RhythmSyed/HMD/NativeBase-KitchenSink-master/assets/contacts/sankhadeep.png

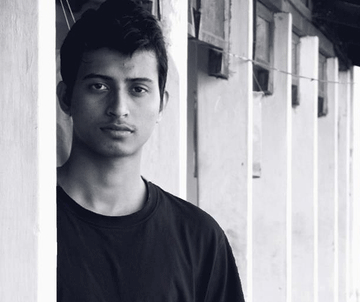
NativeBase-KitchenSink-master/assets/contacts/sankhadeep.png
