RhythmSyed/HMD/NativeBase-KitchenSink-master/assets/contacts/saurabh.png

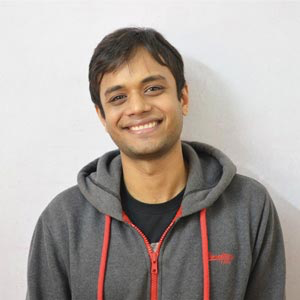
NativeBase-KitchenSink-master/assets/contacts/saurabh.png
