RhythmSyed/HMD/mobileProject/ios/Pods/GoogleMaps/Example/GoogleMapsDemos/Resources/australia-large@2x.png

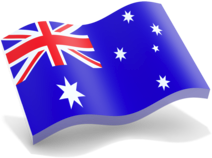
mobileProject/ios/Pods/GoogleMaps/Example/GoogleMapsDemos/Resources/australia-large@2x.png
