RhythmSyed/HMD/mobileProject/ios/Pods/GoogleMaps/Example/GoogleMapsDemos/Resources/newark_nj_1922.jpg

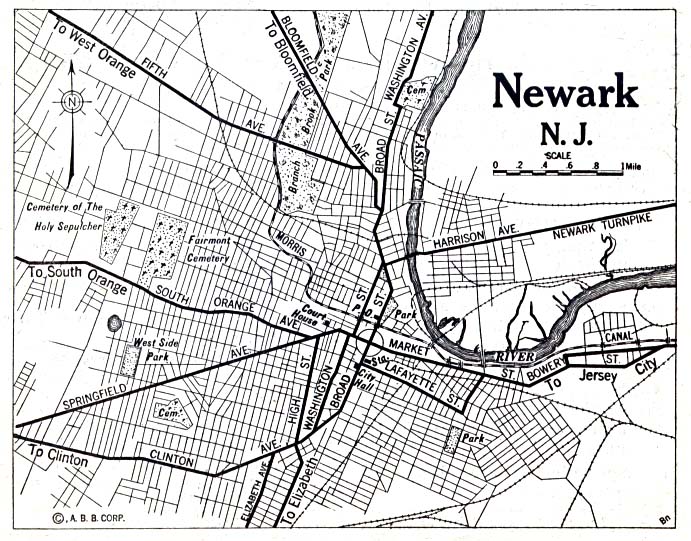
mobileProject/ios/Pods/GoogleMaps/Example/GoogleMapsDemos/Resources/newark_nj_1922.jpg
