RhythmSyed/HMD/NativeBase-KitchenSink-master/assets/camera.png

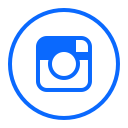
NativeBase-KitchenSink-master/assets/camera.png
