RhythmSyed/HMD/NativeBase-KitchenSink-master/assets/contacts/atul.png

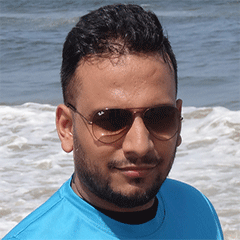
NativeBase-KitchenSink-master/assets/contacts/atul.png
