RhythmSyed/HMD/NativeBase-KitchenSink-master/assets/contacts/himanshu.png

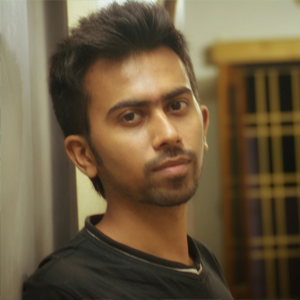
NativeBase-KitchenSink-master/assets/contacts/himanshu.png
