RhythmSyed/HMD/NativeBase-KitchenSink-master/assets/contacts/megha.png

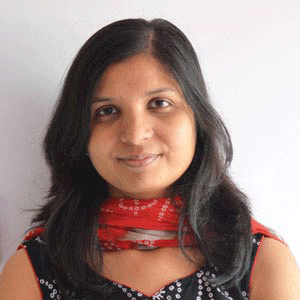
NativeBase-KitchenSink-master/assets/contacts/megha.png
