RhythmSyed/HMD/NativeBase-KitchenSink-master/assets/contacts/pratik.png

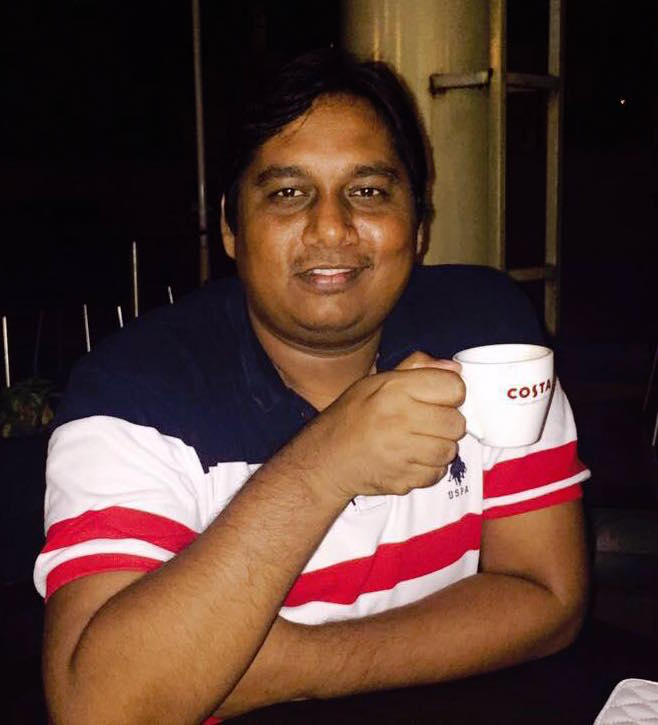
NativeBase-KitchenSink-master/assets/contacts/pratik.png
