RhythmSyed/HMD/NativeBase-KitchenSink-master/assets/contacts/sanket.png

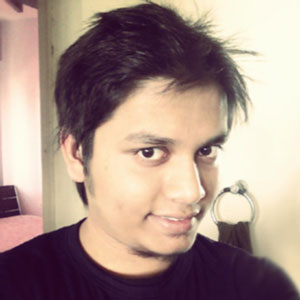
NativeBase-KitchenSink-master/assets/contacts/sanket.png
