RhythmSyed/HMD/NativeBase-KitchenSink-master/assets/contacts/shivraj.png

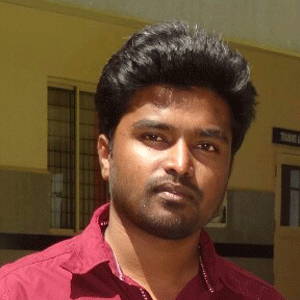
NativeBase-KitchenSink-master/assets/contacts/shivraj.png
