RhythmSyed/HMD/NativeBase-KitchenSink-master/assets/contacts/shruti.png

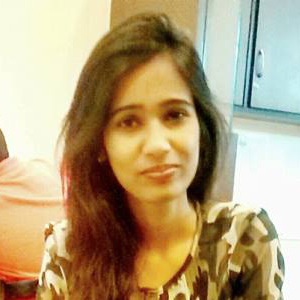
NativeBase-KitchenSink-master/assets/contacts/shruti.png
