RhythmSyed/HMD/NativeBase-KitchenSink-master/assets/contacts/shweta.png

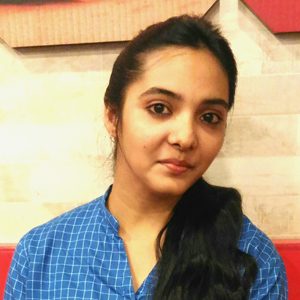
NativeBase-KitchenSink-master/assets/contacts/shweta.png
