RhythmSyed/HMD/NativeBase-KitchenSink-master/assets/contacts/supriya.png

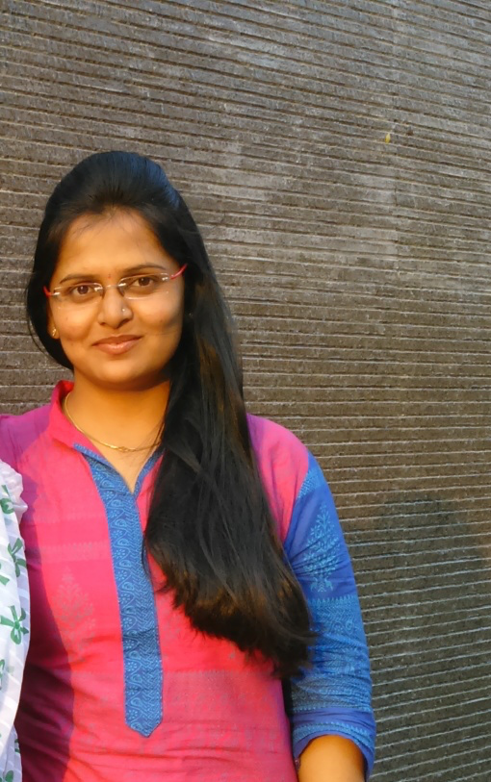
NativeBase-KitchenSink-master/assets/contacts/supriya.png
