RhythmSyed/HMD/NativeBase-KitchenSink-master/assets/contacts/varun.png

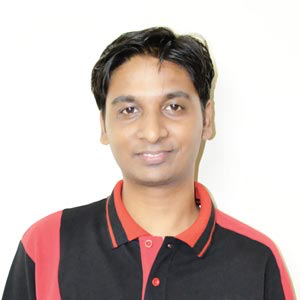
NativeBase-KitchenSink-master/assets/contacts/varun.png
