RhythmSyed/HMD/NativeBase-KitchenSink-master/assets/drawer-cover.png

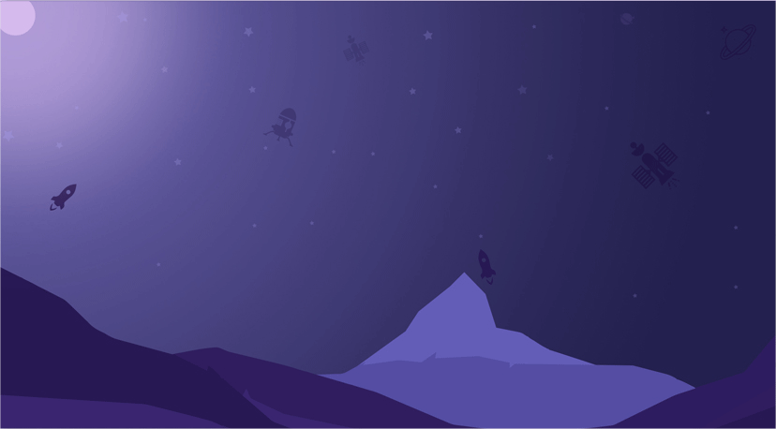
NativeBase-KitchenSink-master/assets/drawer-cover.png
