RhythmSyed/HMD/NativeBase-KitchenSink-master/assets/header-transparent.png

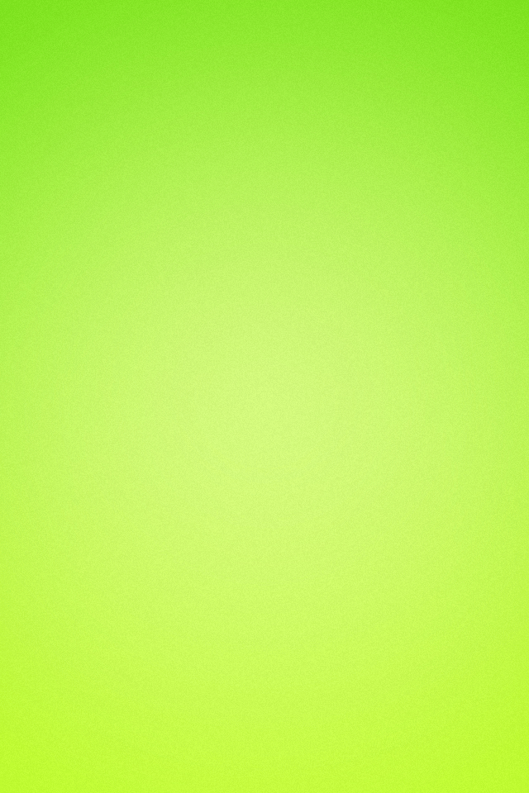
NativeBase-KitchenSink-master/assets/header-transparent.png
