RhythmSyed/HMD/NativeBase-KitchenSink-master/assets/launchscreen-bg.png

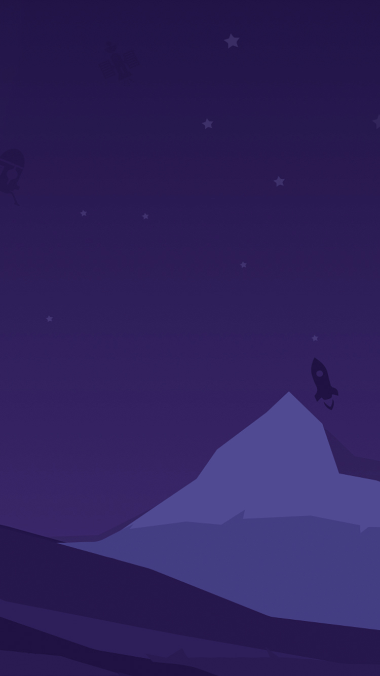
NativeBase-KitchenSink-master/assets/launchscreen-bg.png
