RhythmSyed/HMD/NativeBase-KitchenSink-master/assets/swiper-1.png

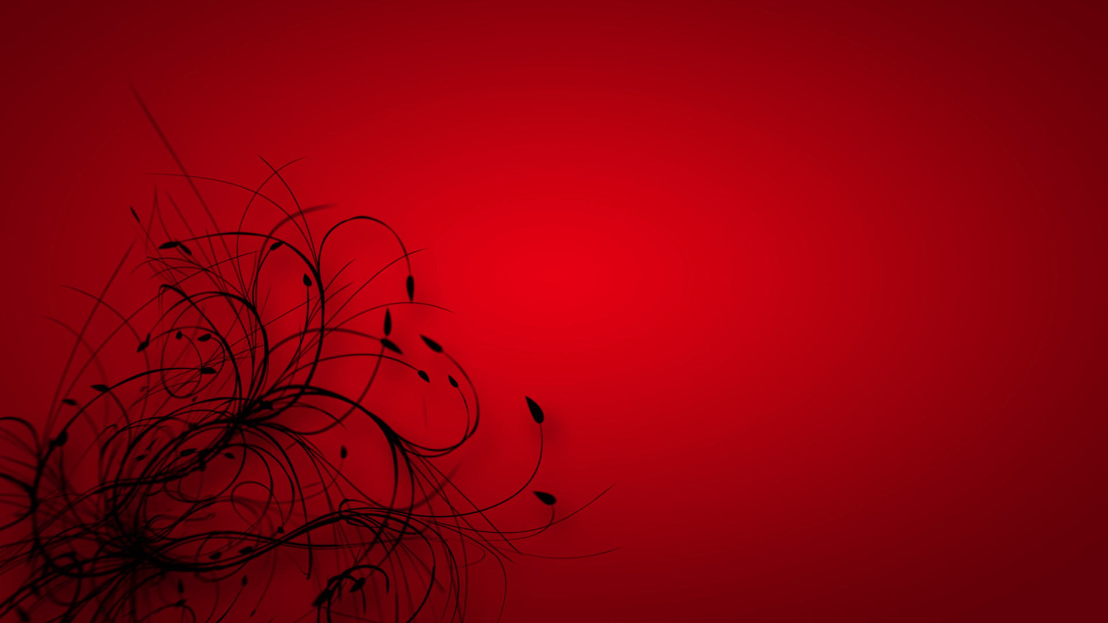
NativeBase-KitchenSink-master/assets/swiper-1.png
