RhythmSyed/HMD/NativeBase-KitchenSink-master/assets/swiper-3.png

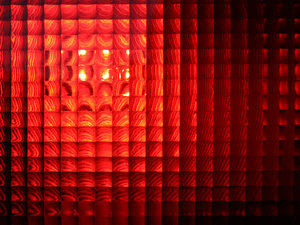
NativeBase-KitchenSink-master/assets/swiper-3.png
