RhythmSyed/HMD/NativeBase-KitchenSink-master/assets/swiper-4.png

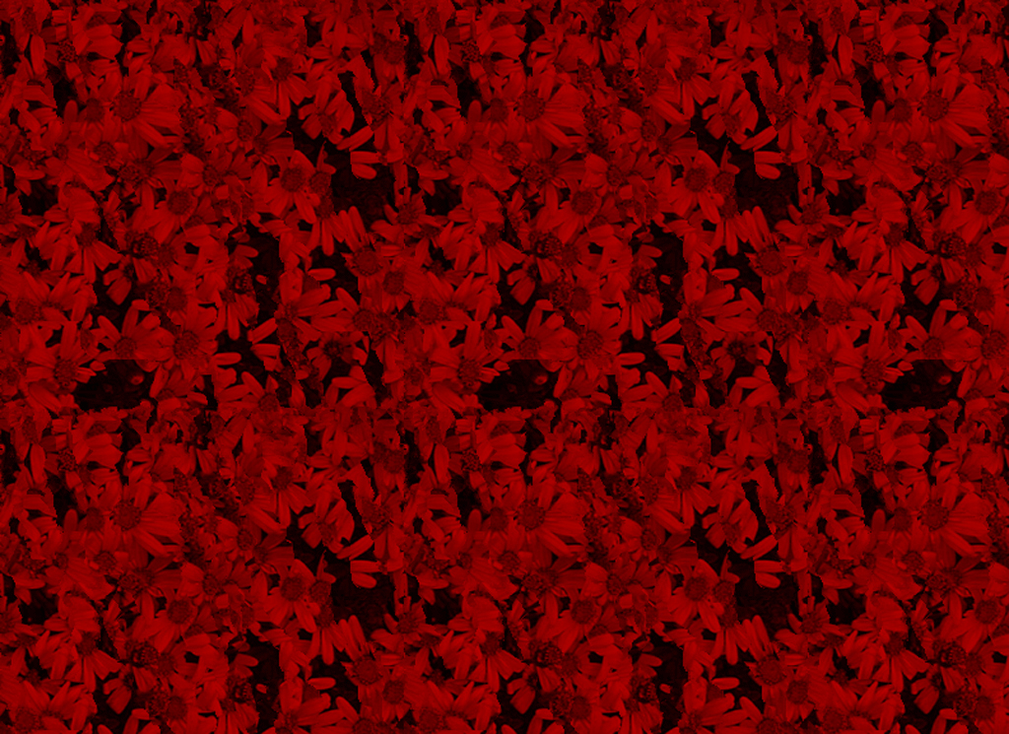
NativeBase-KitchenSink-master/assets/swiper-4.png
