RhythmSyed/HMD/NativeBase-KitchenSink-master/assets/web-cover1.png

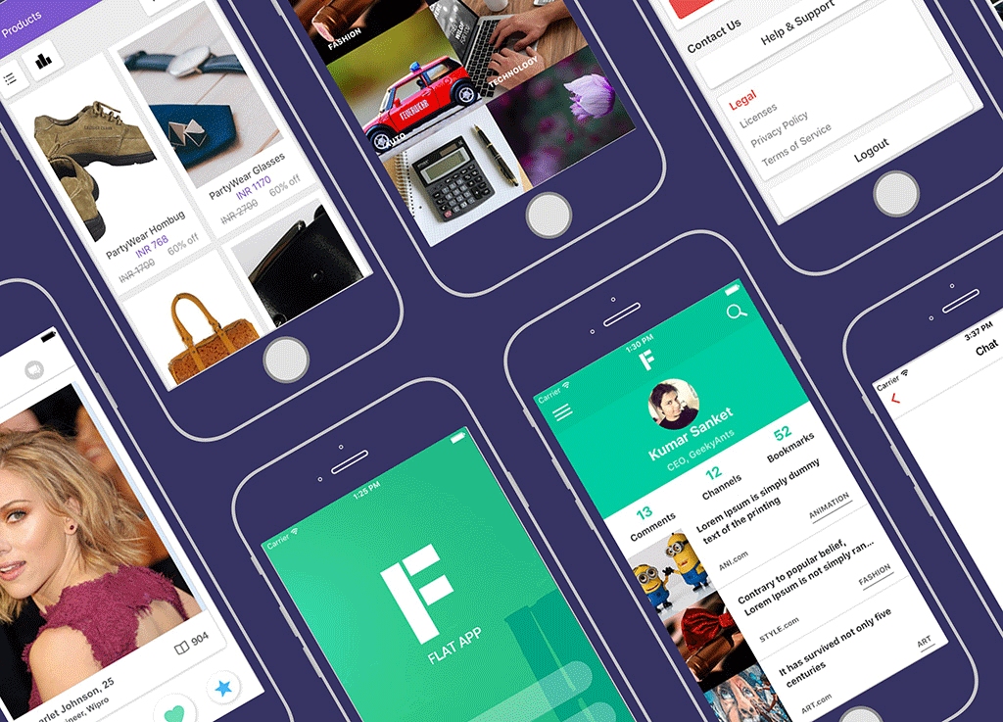
NativeBase-KitchenSink-master/assets/web-cover1.png
