RhythmSyed/HMD/NativeBase-KitchenSink-master/screenshots/Android.gif

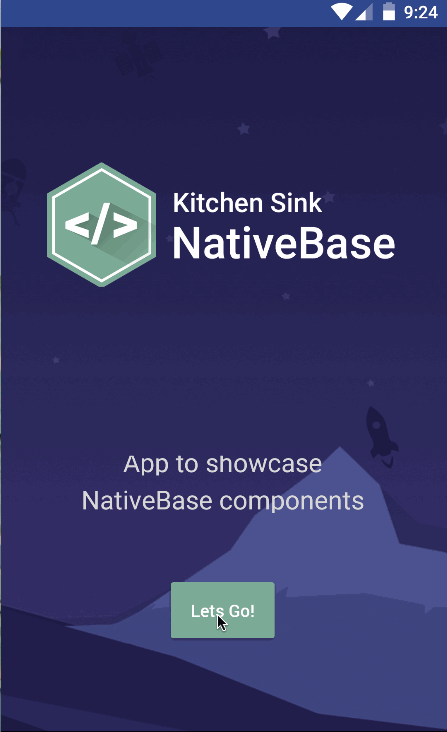
NativeBase-KitchenSink-master/screenshots/Android.gif
