RhythmSyed/HMD/NativeBase-KitchenSink-master/screenshots/android/accordion-custom-header-content.gif

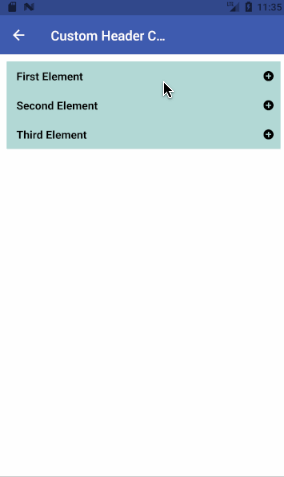
NativeBase-KitchenSink-master/screenshots/android/accordion-custom-header-content.gif
