RhythmSyed/HMD/NativeBase-KitchenSink-master/screenshots/android/accordion-header-content-style.gif

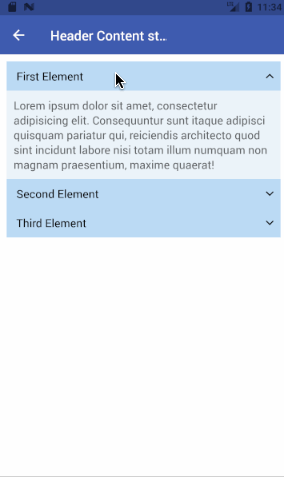
NativeBase-KitchenSink-master/screenshots/android/accordion-header-content-style.gif
