RhythmSyed/HMD/NativeBase-KitchenSink-master/screenshots/android/accordion.gif

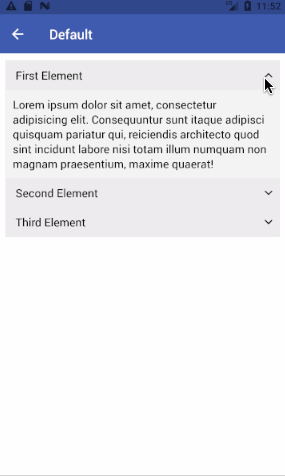
NativeBase-KitchenSink-master/screenshots/android/accordion.gif
