RhythmSyed/HMD/NativeBase-KitchenSink-master/screenshots/android/actionsheet.gif

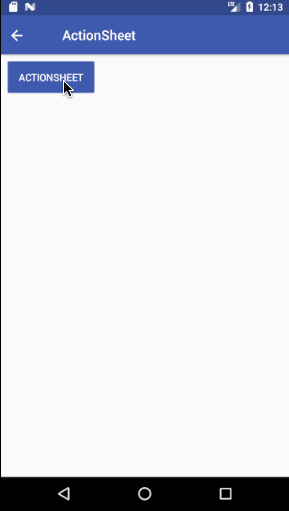
NativeBase-KitchenSink-master/screenshots/android/actionsheet.gif
