RhythmSyed/HMD/NativeBase-KitchenSink-master/screenshots/android/anatomy.png

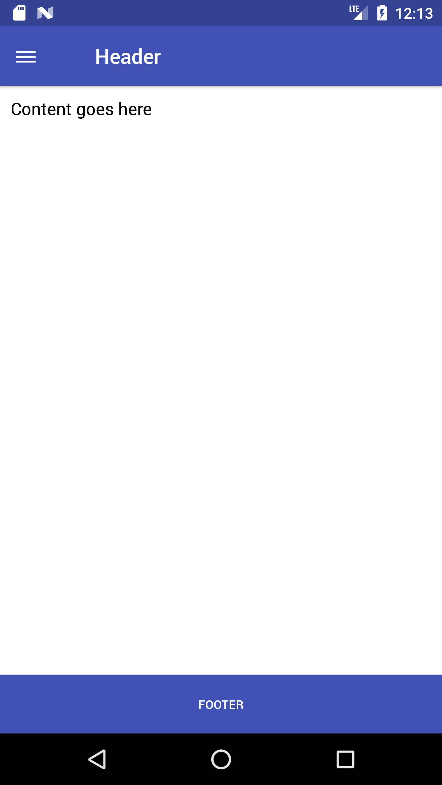
NativeBase-KitchenSink-master/screenshots/android/anatomy.png
