RhythmSyed/HMD/NativeBase-KitchenSink-master/screenshots/android/button-block.png

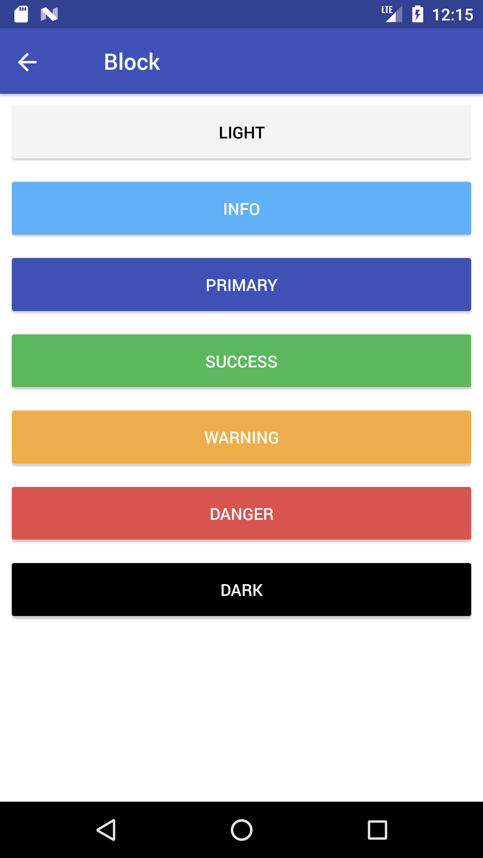
NativeBase-KitchenSink-master/screenshots/android/button-block.png
