RhythmSyed/HMD/NativeBase-KitchenSink-master/screenshots/android/button-disabled.png

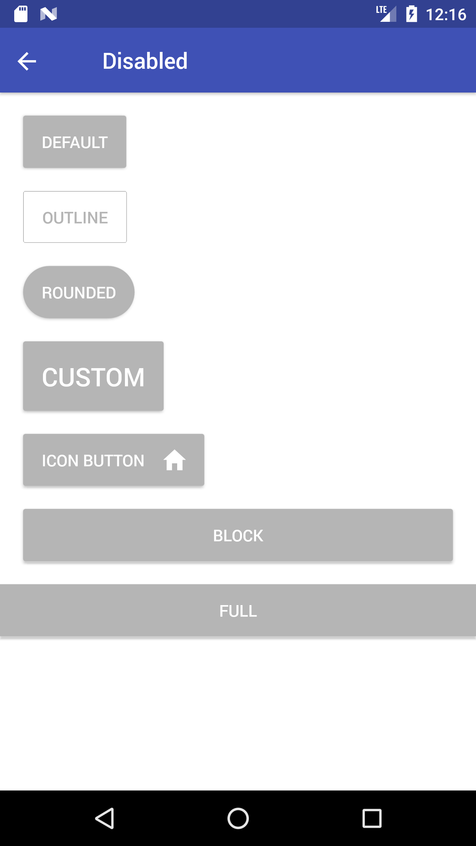
NativeBase-KitchenSink-master/screenshots/android/button-disabled.png
