RhythmSyed/HMD/NativeBase-KitchenSink-master/screenshots/android/button-full.png

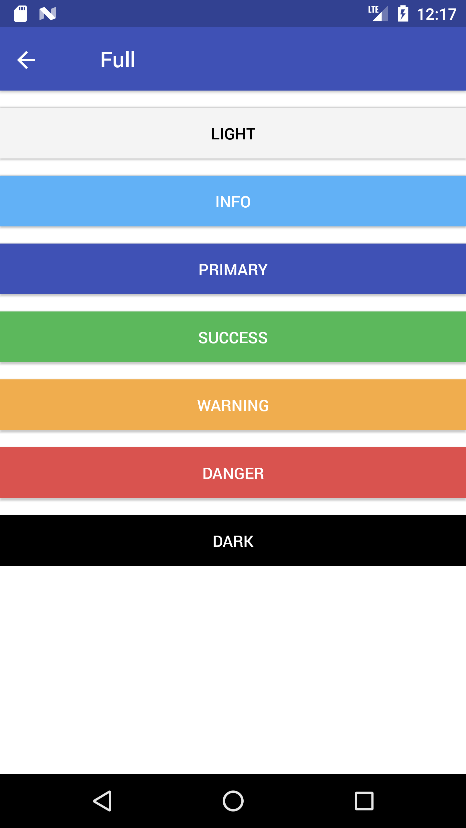
NativeBase-KitchenSink-master/screenshots/android/button-full.png
