RhythmSyed/HMD/NativeBase-KitchenSink-master/screenshots/android/button-outline.png

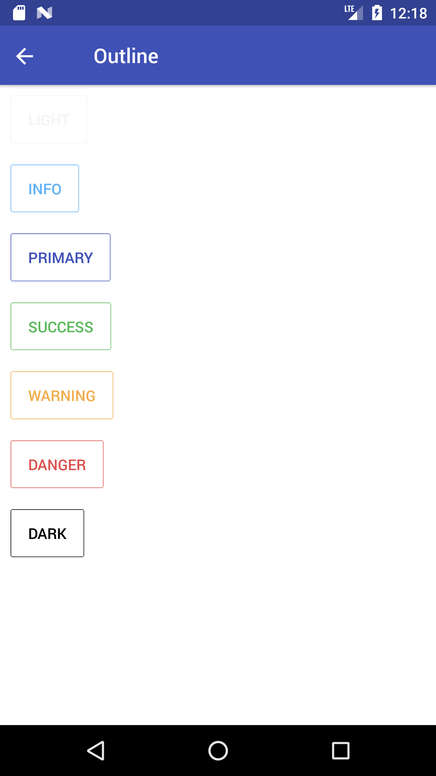
NativeBase-KitchenSink-master/screenshots/android/button-outline.png
