RhythmSyed/HMD/NativeBase-KitchenSink-master/screenshots/android/button-size.png

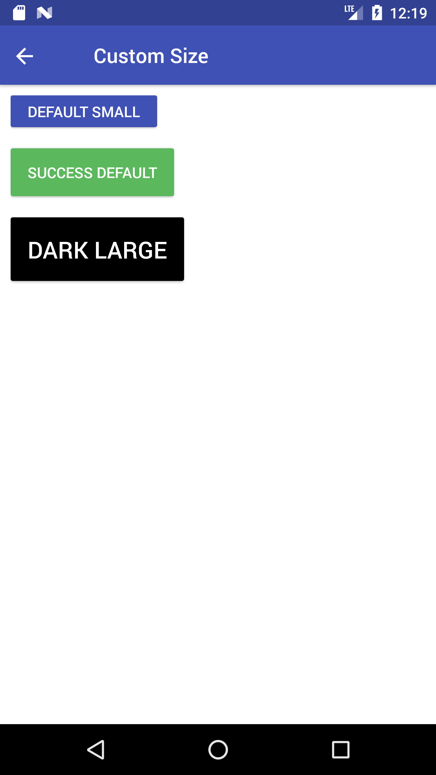
NativeBase-KitchenSink-master/screenshots/android/button-size.png
