RhythmSyed/HMD/NativeBase-KitchenSink-master/screenshots/android/button-transparent.png

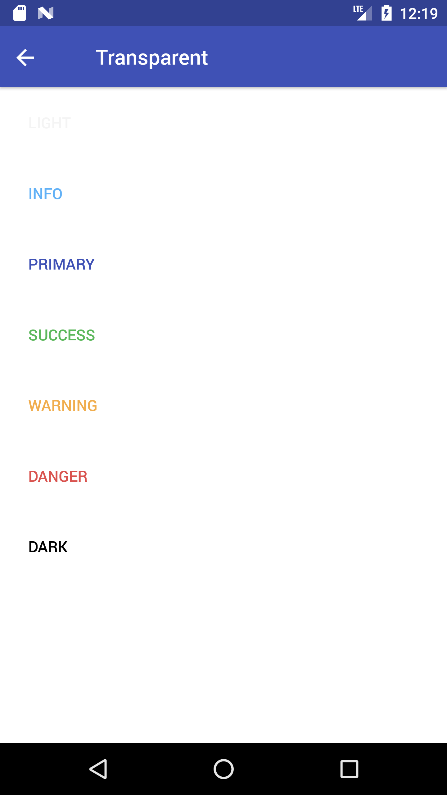
NativeBase-KitchenSink-master/screenshots/android/button-transparent.png
