RhythmSyed/HMD/NativeBase-KitchenSink-master/screenshots/android/card-basic.png

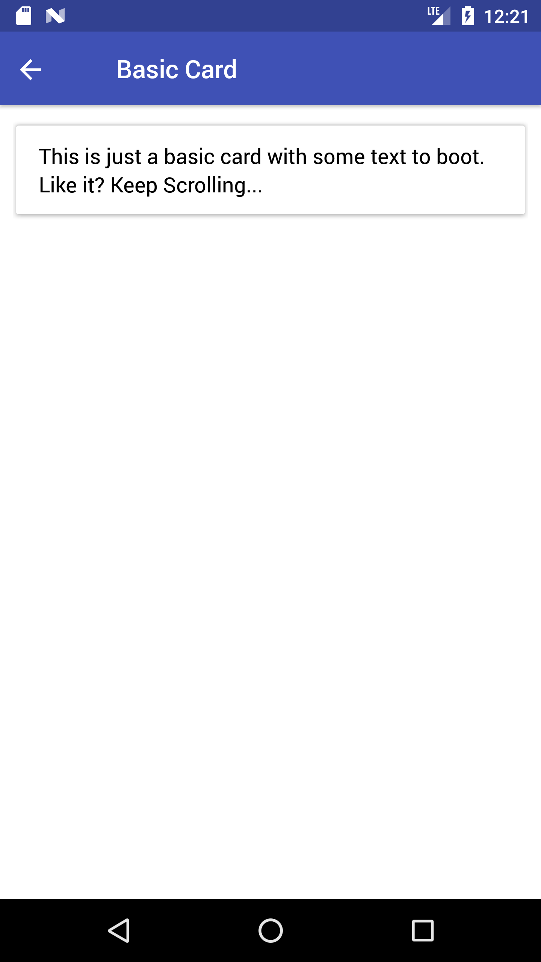
NativeBase-KitchenSink-master/screenshots/android/card-basic.png
