RhythmSyed/HMD/NativeBase-KitchenSink-master/screenshots/android/card-bordered.png

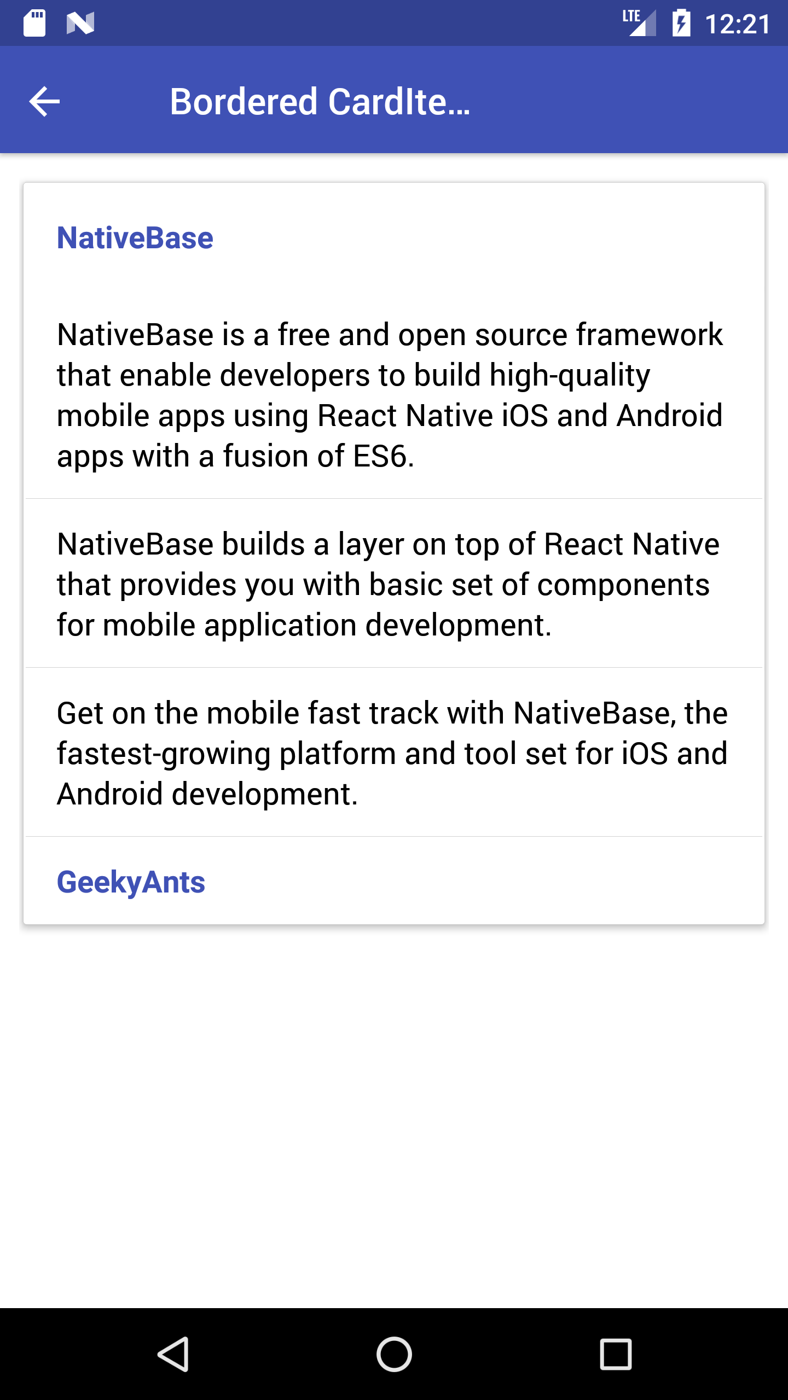
NativeBase-KitchenSink-master/screenshots/android/card-bordered.png
