RhythmSyed/HMD/NativeBase-KitchenSink-master/screenshots/android/card-button.gif

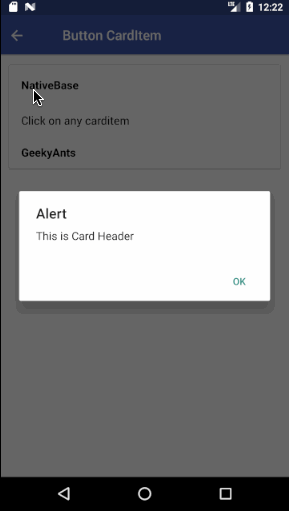
NativeBase-KitchenSink-master/screenshots/android/card-button.gif
