RhythmSyed/HMD/NativeBase-KitchenSink-master/screenshots/android/card-custom-border-radius.png

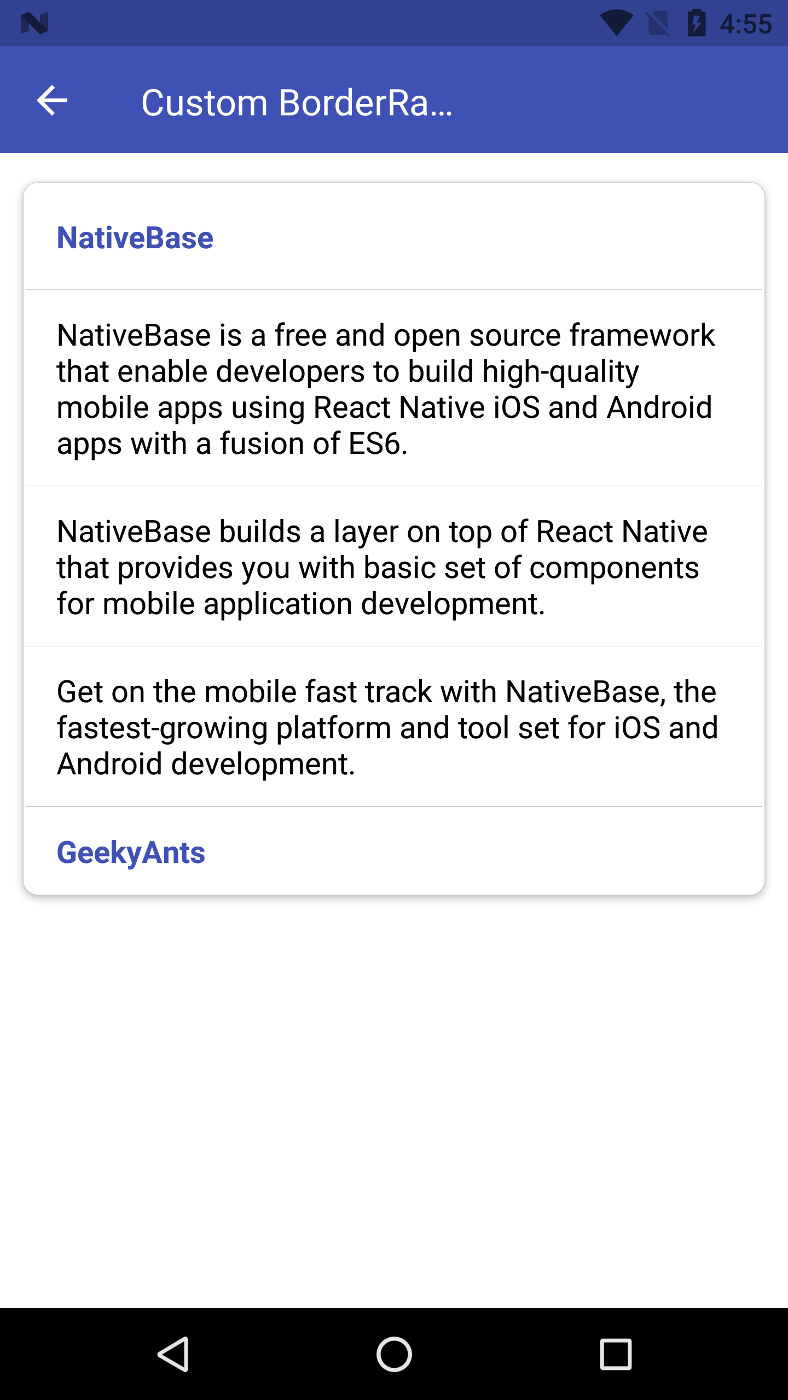
NativeBase-KitchenSink-master/screenshots/android/card-custom-border-radius.png
