RhythmSyed/HMD/NativeBase-KitchenSink-master/screenshots/android/card-image.png

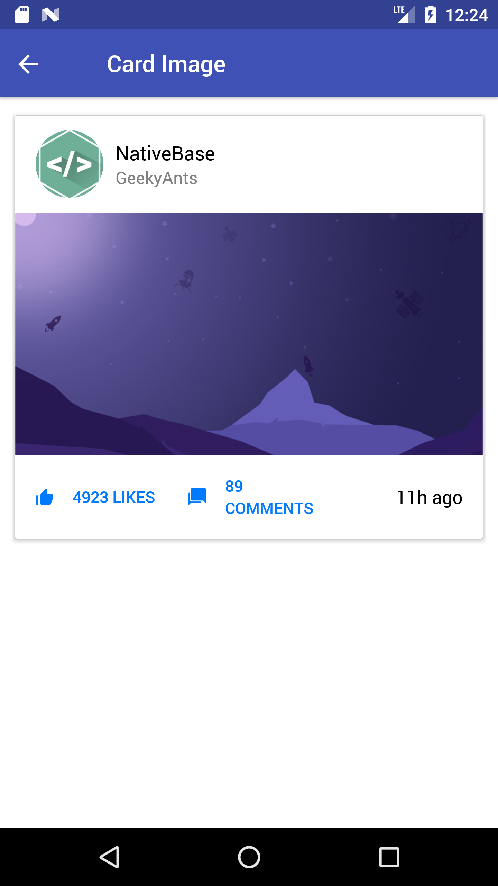
NativeBase-KitchenSink-master/screenshots/android/card-image.png
