RhythmSyed/HMD/NativeBase-KitchenSink-master/screenshots/android/card-list.png

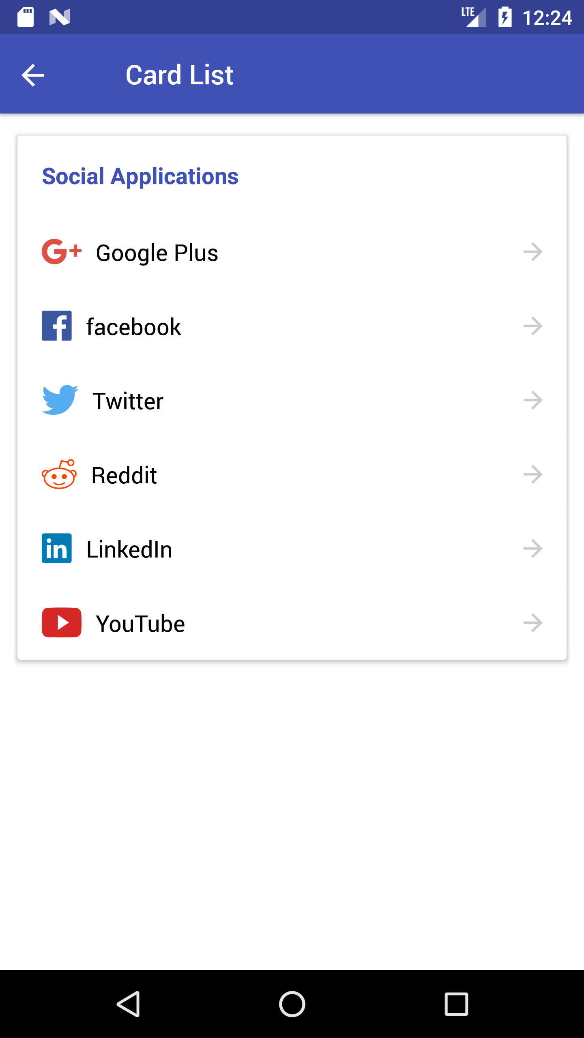
NativeBase-KitchenSink-master/screenshots/android/card-list.png
