RhythmSyed/HMD/NativeBase-KitchenSink-master/screenshots/android/card-showcase.png

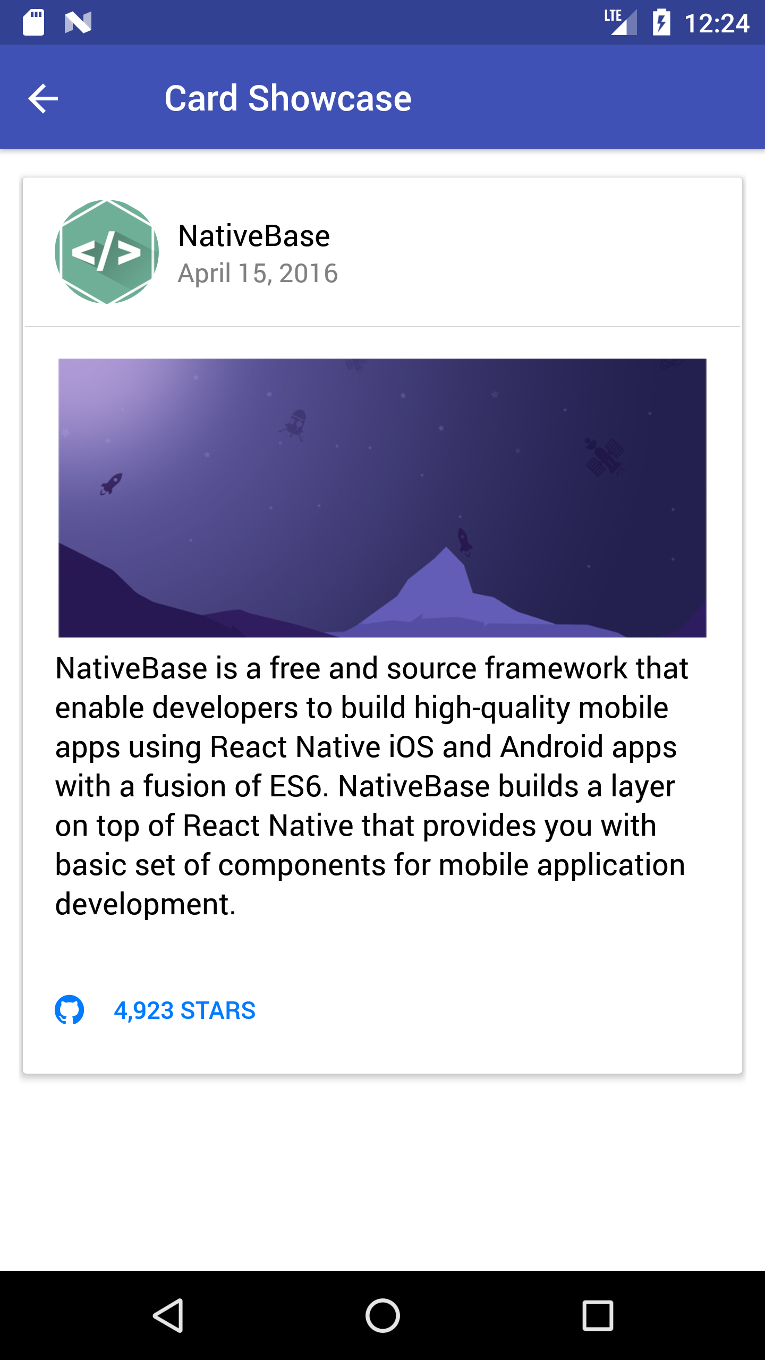
NativeBase-KitchenSink-master/screenshots/android/card-showcase.png
