RhythmSyed/HMD/NativeBase-KitchenSink-master/screenshots/android/card-transparent.png

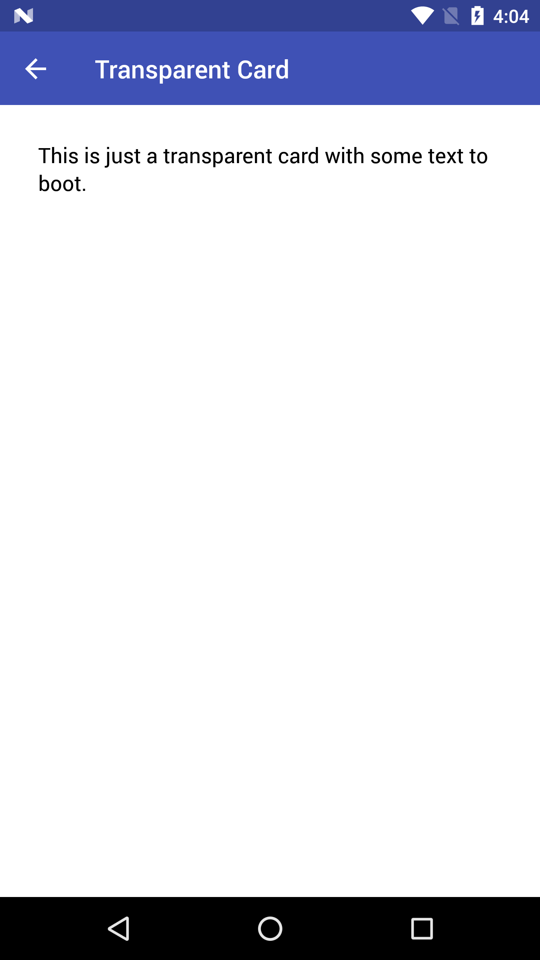
NativeBase-KitchenSink-master/screenshots/android/card-transparent.png
