RhythmSyed/HMD/NativeBase-KitchenSink-master/screenshots/android/checkbox.png

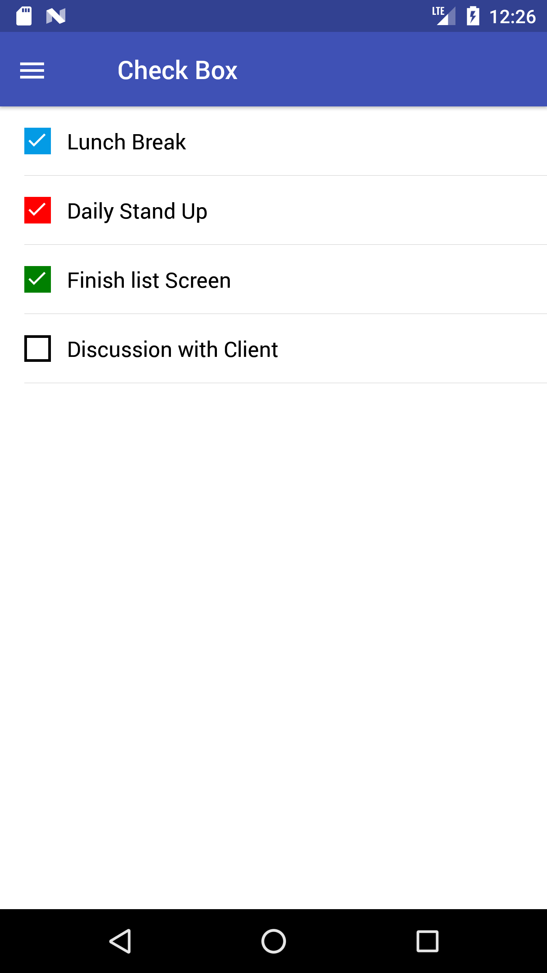
NativeBase-KitchenSink-master/screenshots/android/checkbox.png
