RhythmSyed/HMD/NativeBase-KitchenSink-master/screenshots/android/deckswiper-advanced.gif

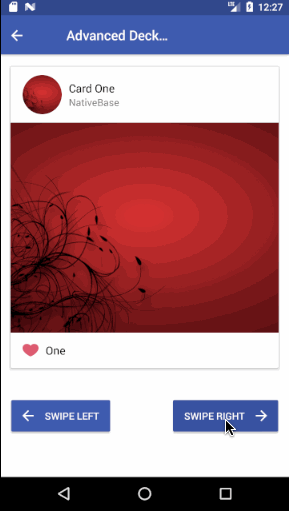
NativeBase-KitchenSink-master/screenshots/android/deckswiper-advanced.gif
