RhythmSyed/HMD/NativeBase-KitchenSink-master/screenshots/android/deckswiper.gif

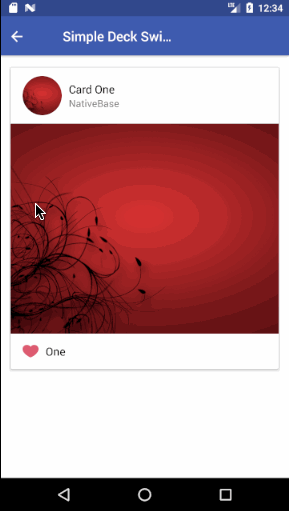
NativeBase-KitchenSink-master/screenshots/android/deckswiper.gif
