RhythmSyed/HMD/NativeBase-KitchenSink-master/screenshots/android/drawer.png

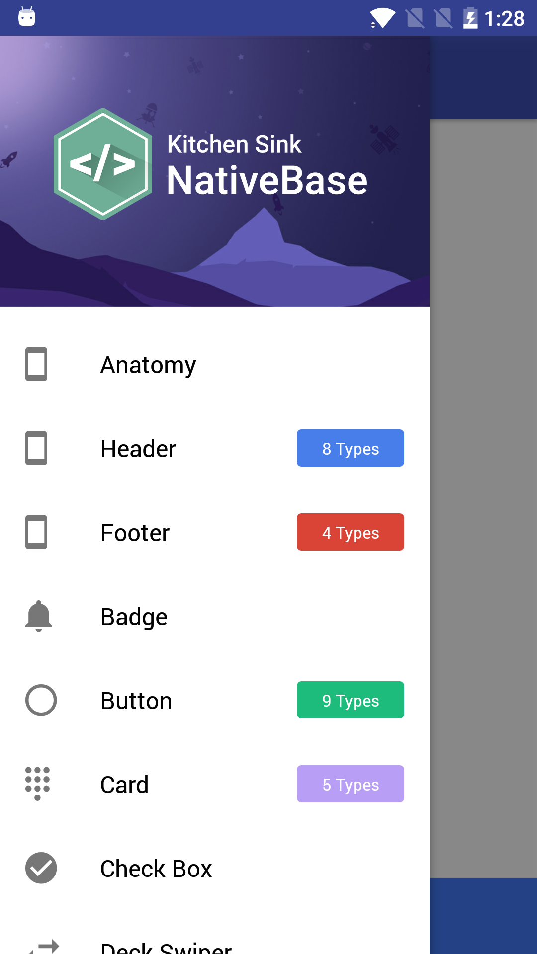
NativeBase-KitchenSink-master/screenshots/android/drawer.png
