RhythmSyed/HMD/NativeBase-KitchenSink-master/screenshots/android/FAB-multiple.gif

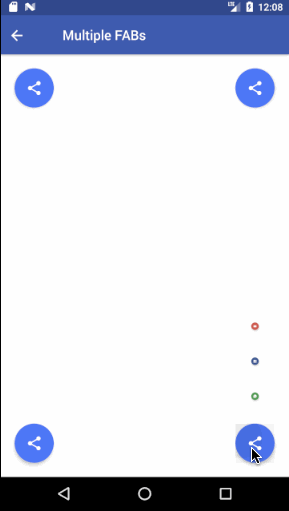
NativeBase-KitchenSink-master/screenshots/android/FAB-multiple.gif
