RhythmSyed/HMD/NativeBase-KitchenSink-master/screenshots/android/FAB-single.gif

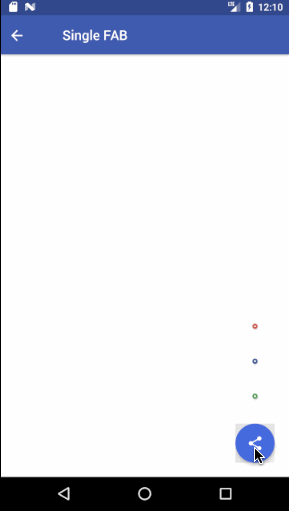
NativeBase-KitchenSink-master/screenshots/android/FAB-single.gif
