RhythmSyed/HMD/NativeBase-KitchenSink-master/screenshots/android/footer-text.png

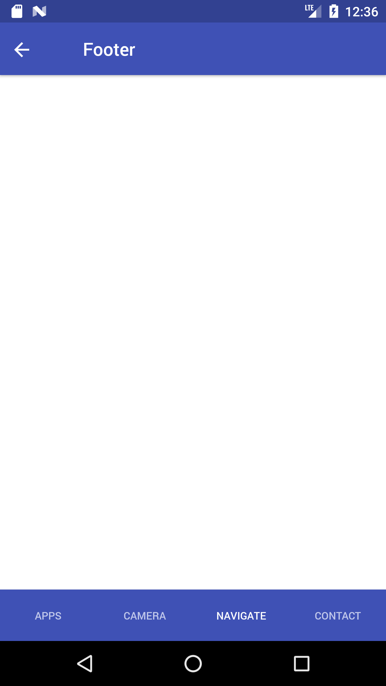
NativeBase-KitchenSink-master/screenshots/android/footer-text.png
