RhythmSyed/HMD/NativeBase-KitchenSink-master/screenshots/android/header-custom.png

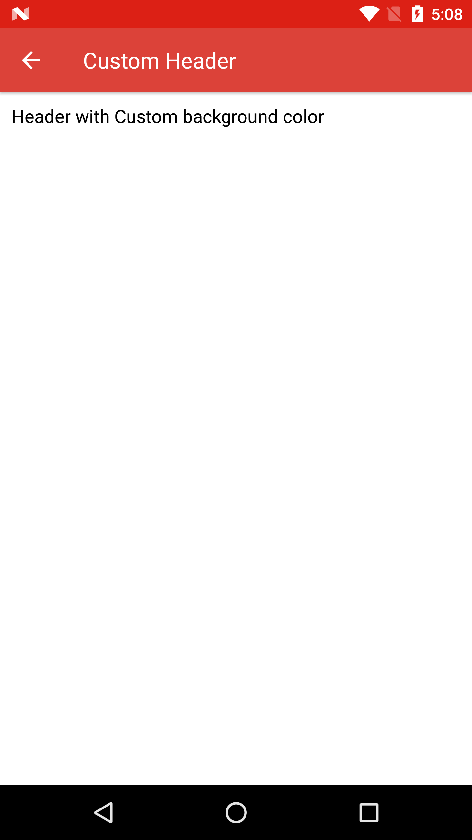
NativeBase-KitchenSink-master/screenshots/android/header-custom.png
