RhythmSyed/HMD/NativeBase-KitchenSink-master/screenshots/android/header-noleft.png

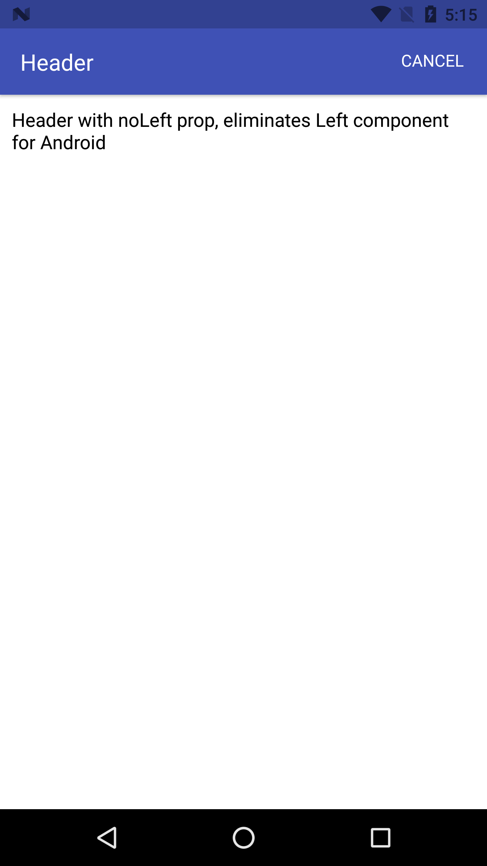
NativeBase-KitchenSink-master/screenshots/android/header-noleft.png
