RhythmSyed/HMD/NativeBase-KitchenSink-master/screenshots/android/header-noshadow.png

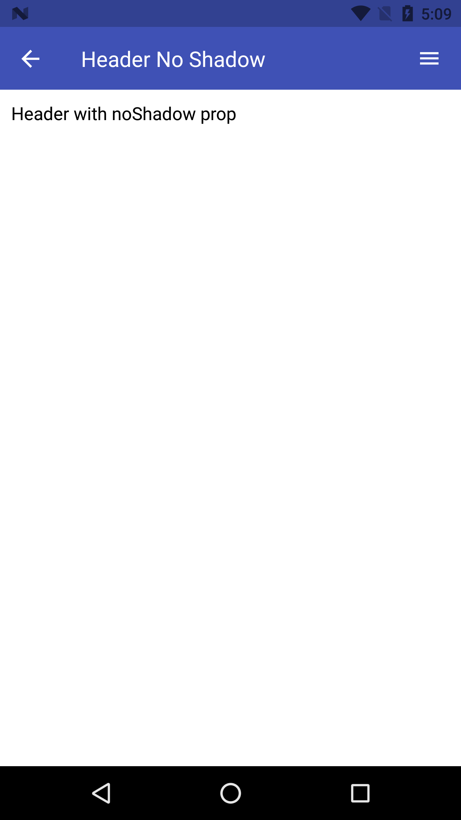
NativeBase-KitchenSink-master/screenshots/android/header-noshadow.png
