RhythmSyed/HMD/NativeBase-KitchenSink-master/screenshots/android/header-span.png

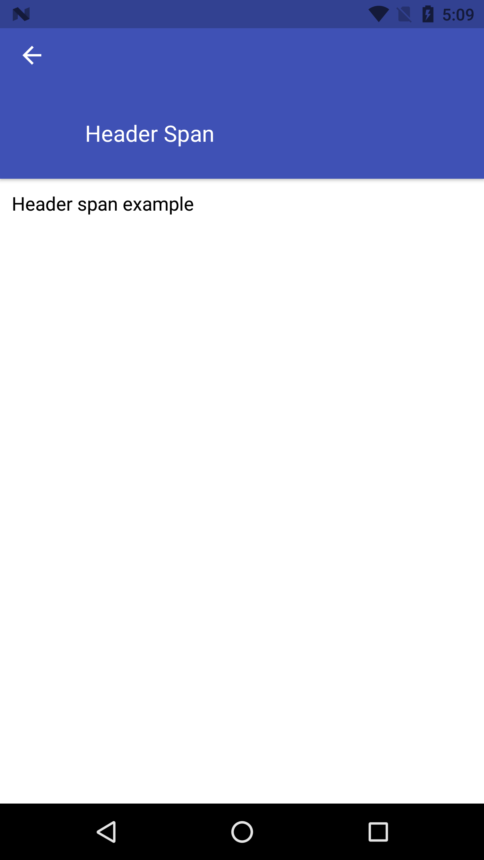
NativeBase-KitchenSink-master/screenshots/android/header-span.png
