RhythmSyed/HMD/NativeBase-KitchenSink-master/screenshots/android/header-with-title.png

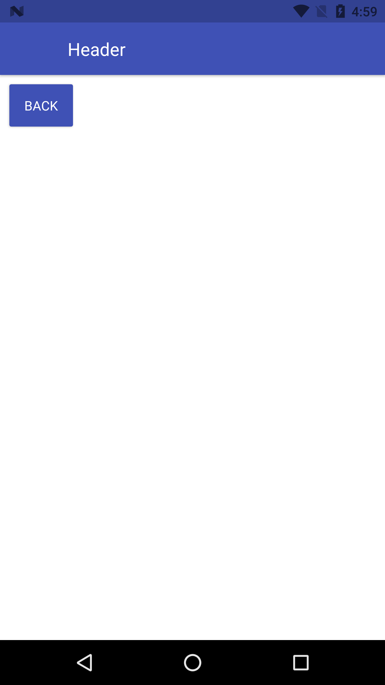
NativeBase-KitchenSink-master/screenshots/android/header-with-title.png
