RhythmSyed/HMD/NativeBase-KitchenSink-master/screenshots/android/input-fixed.png

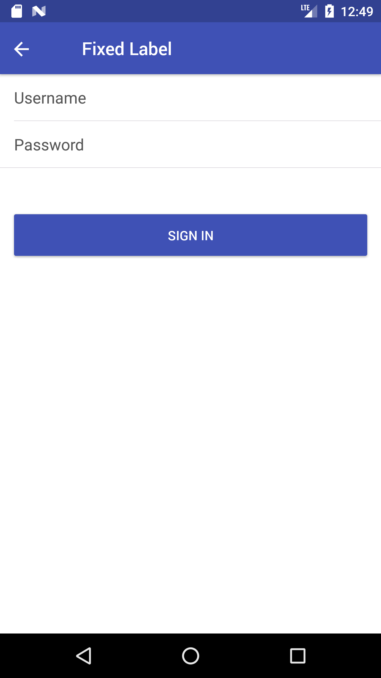
NativeBase-KitchenSink-master/screenshots/android/input-fixed.png
