RhythmSyed/HMD/NativeBase-KitchenSink-master/screenshots/android/input-floating.gif

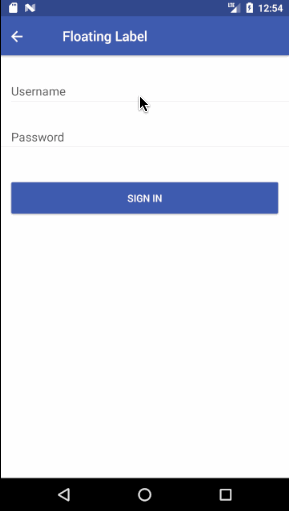
NativeBase-KitchenSink-master/screenshots/android/input-floating.gif
