RhythmSyed/HMD/NativeBase-KitchenSink-master/screenshots/android/input-picker.gif

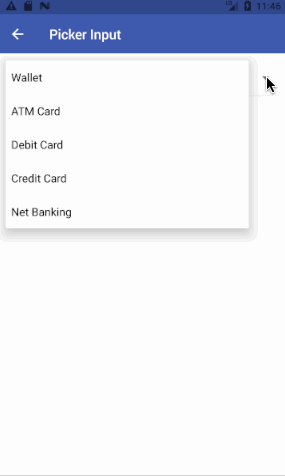
NativeBase-KitchenSink-master/screenshots/android/input-picker.gif
