RhythmSyed/HMD/NativeBase-KitchenSink-master/screenshots/android/layout.png

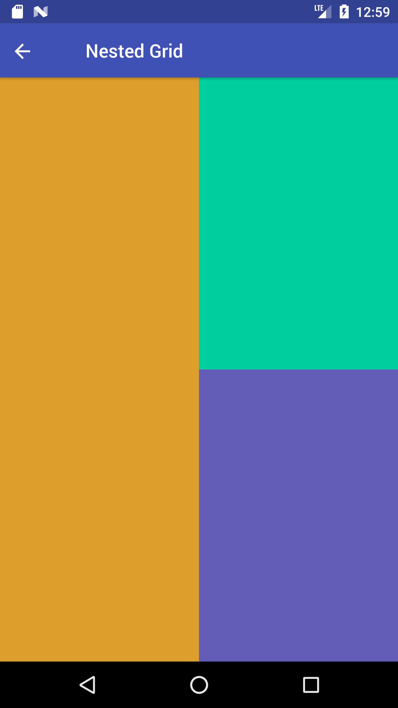
NativeBase-KitchenSink-master/screenshots/android/layout.png
