RhythmSyed/HMD/NativeBase-KitchenSink-master/screenshots/android/list-basic.png

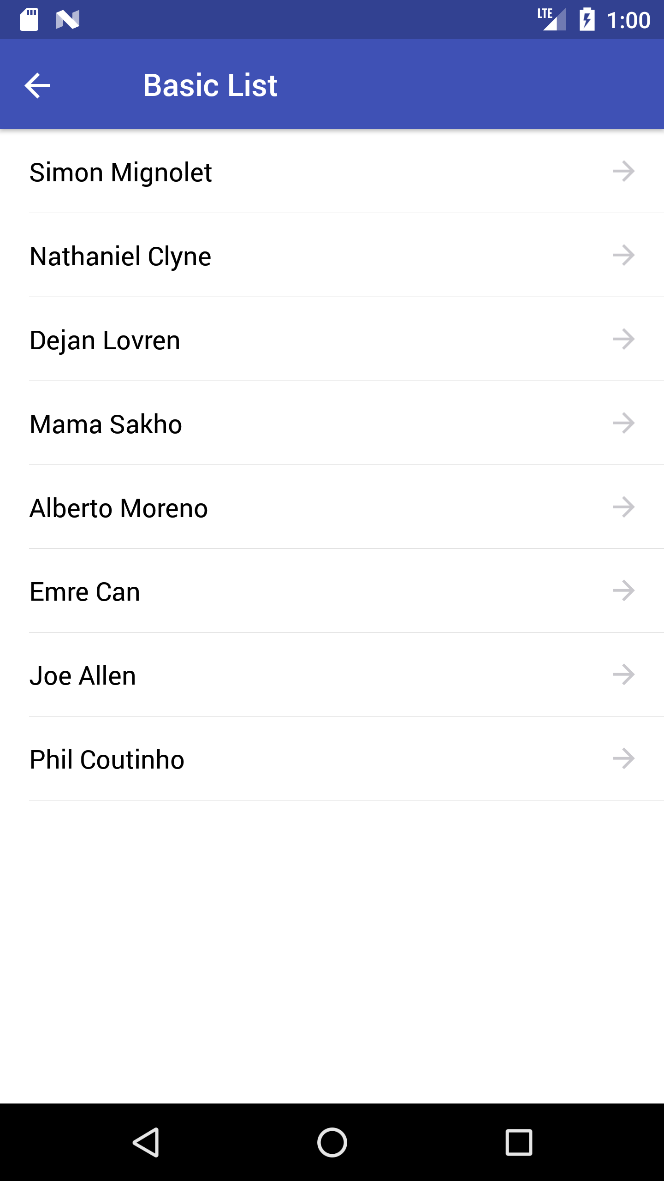
NativeBase-KitchenSink-master/screenshots/android/list-basic.png
