RhythmSyed/HMD/NativeBase-KitchenSink-master/screenshots/android/list-divider.png

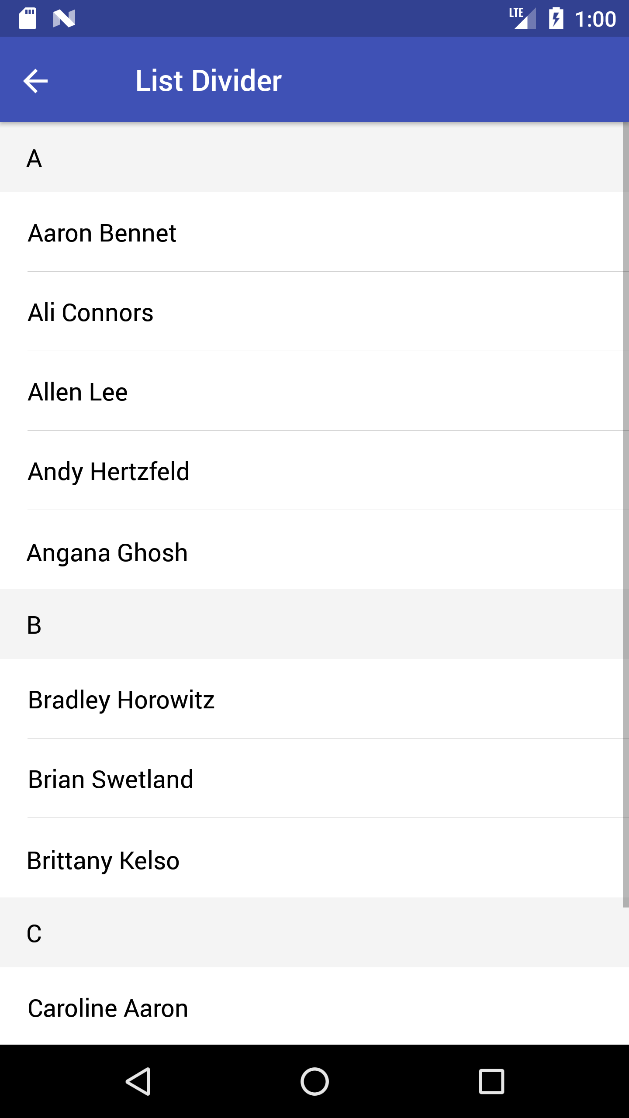
NativeBase-KitchenSink-master/screenshots/android/list-divider.png
