RhythmSyed/HMD/NativeBase-KitchenSink-master/screenshots/android/list-dynamic.png

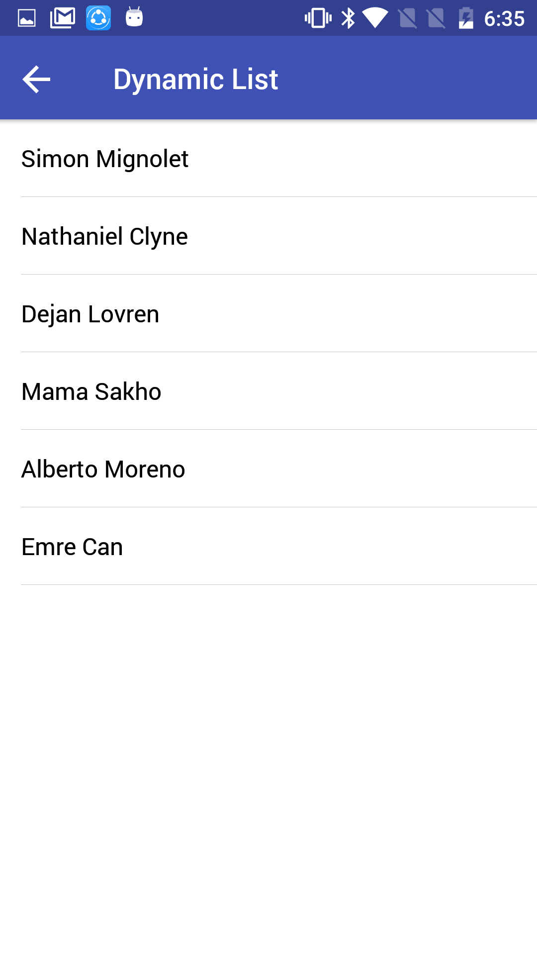
NativeBase-KitchenSink-master/screenshots/android/list-dynamic.png
