RhythmSyed/HMD/NativeBase-KitchenSink-master/screenshots/android/list-header.png

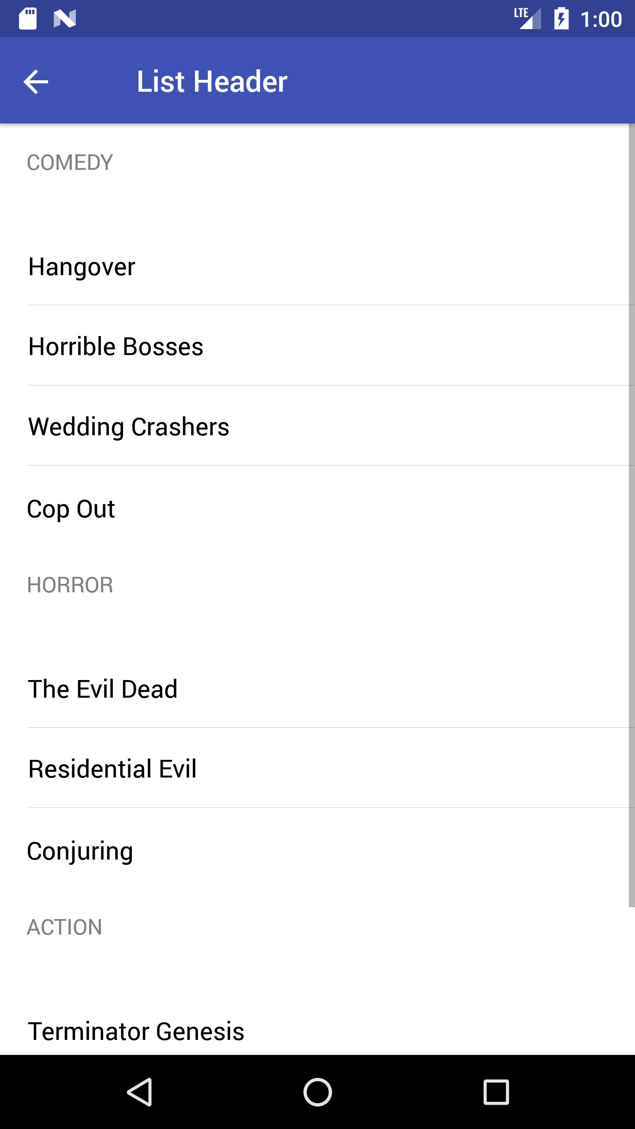
NativeBase-KitchenSink-master/screenshots/android/list-header.png
