RhythmSyed/HMD/NativeBase-KitchenSink-master/screenshots/android/list-separator.png

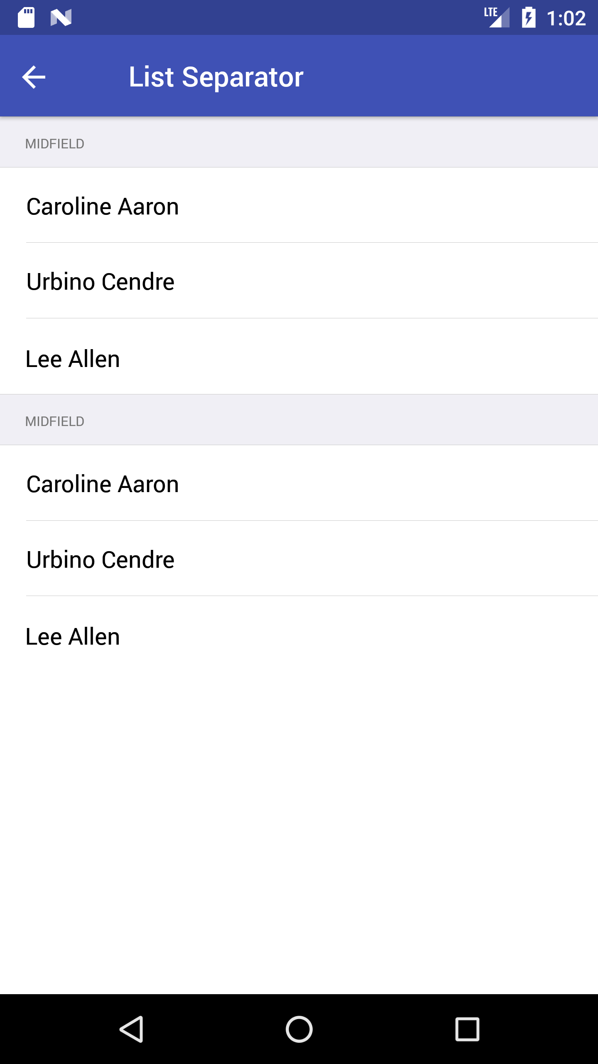
NativeBase-KitchenSink-master/screenshots/android/list-separator.png
