RhythmSyed/HMD/NativeBase-KitchenSink-master/screenshots/android/list-swipe-multiple.gif

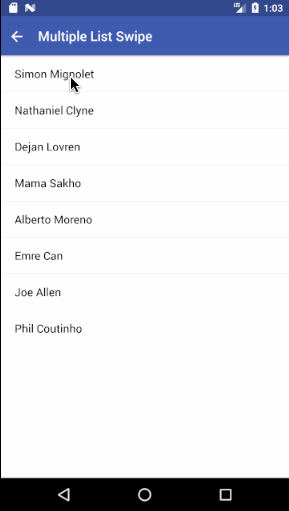
NativeBase-KitchenSink-master/screenshots/android/list-swipe-multiple.gif
