RhythmSyed/HMD/NativeBase-KitchenSink-master/screenshots/android/list-swipe-single-row-custom-style.gif

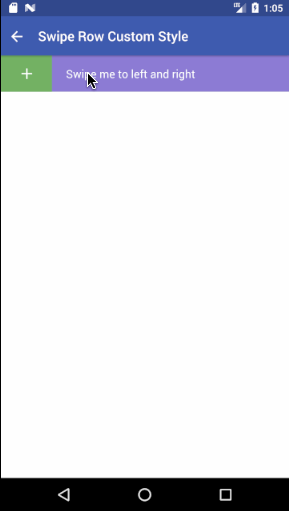
NativeBase-KitchenSink-master/screenshots/android/list-swipe-single-row-custom-style.gif
