RhythmSyed/HMD/NativeBase-KitchenSink-master/screenshots/android/list-swipe-single-row.gif

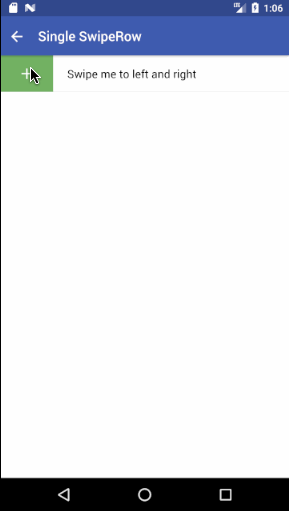
NativeBase-KitchenSink-master/screenshots/android/list-swipe-single-row.gif
