RhythmSyed/HMD/NativeBase-KitchenSink-master/screenshots/android/list-thumbnail.png

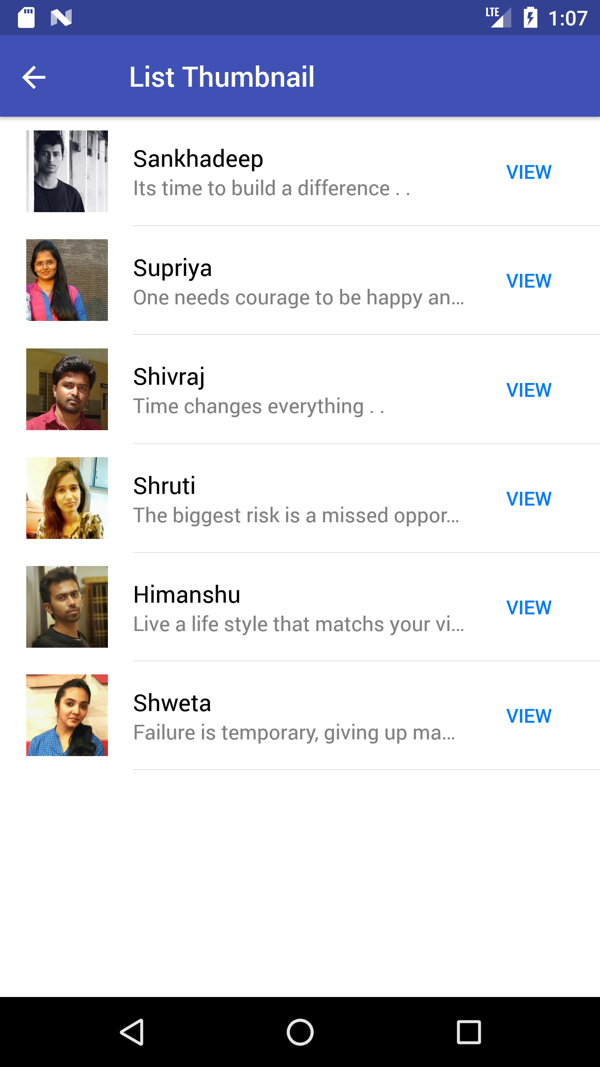
NativeBase-KitchenSink-master/screenshots/android/list-thumbnail.png
