RhythmSyed/HMD/NativeBase-KitchenSink-master/screenshots/android/picker.gif

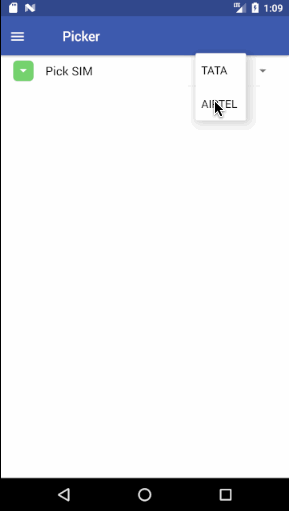
NativeBase-KitchenSink-master/screenshots/android/picker.gif
