RhythmSyed/HMD/NativeBase-KitchenSink-master/screenshots/android/radio-custom.png

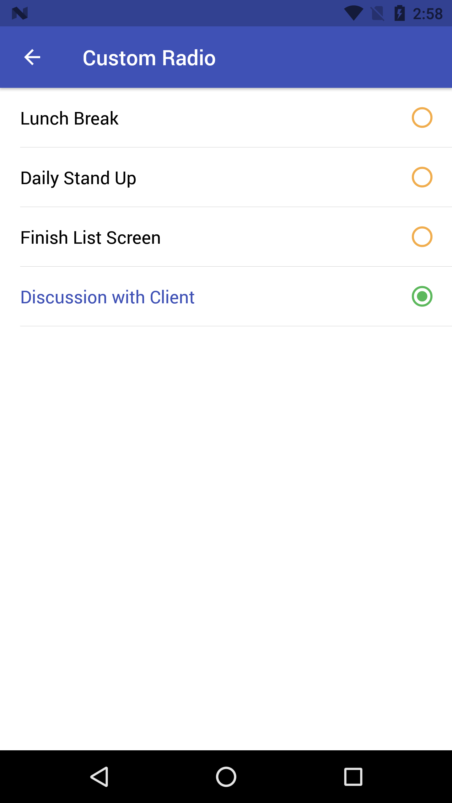
NativeBase-KitchenSink-master/screenshots/android/radio-custom.png
