RhythmSyed/HMD/NativeBase-KitchenSink-master/screenshots/android/searchbar.png

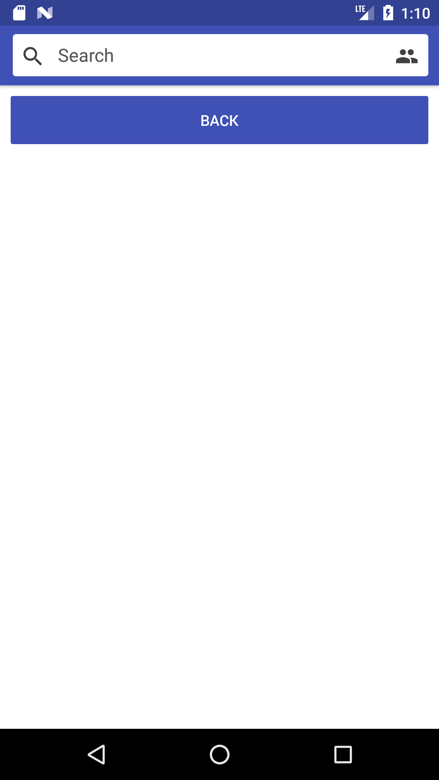
NativeBase-KitchenSink-master/screenshots/android/searchbar.png
