RhythmSyed/HMD/NativeBase-KitchenSink-master/screenshots/android/segment-inside-header.gif

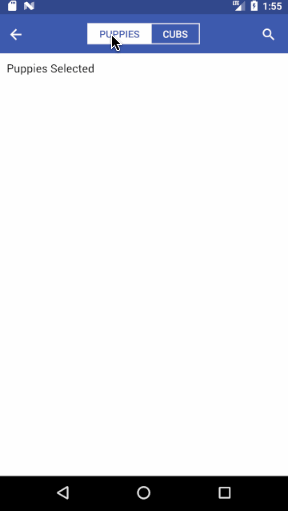
NativeBase-KitchenSink-master/screenshots/android/segment-inside-header.gif
