RhythmSyed/HMD/NativeBase-KitchenSink-master/screenshots/android/segment-outside-header.gif

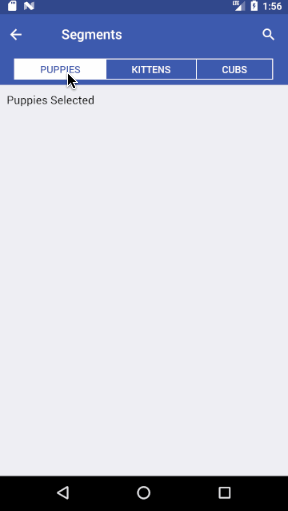
NativeBase-KitchenSink-master/screenshots/android/segment-outside-header.gif
