RhythmSyed/HMD/NativeBase-KitchenSink-master/screenshots/android/tabs-advanced.gif

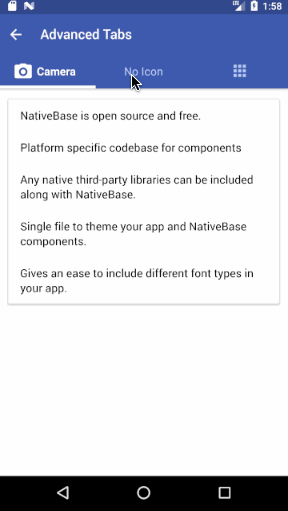
NativeBase-KitchenSink-master/screenshots/android/tabs-advanced.gif
