RhythmSyed/HMD/NativeBase-KitchenSink-master/screenshots/android/tabs-scrollable.gif

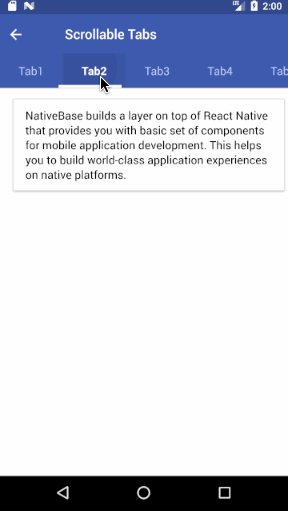
NativeBase-KitchenSink-master/screenshots/android/tabs-scrollable.gif
