RhythmSyed/HMD/NativeBase-KitchenSink-master/screenshots/android/thumbnail.png

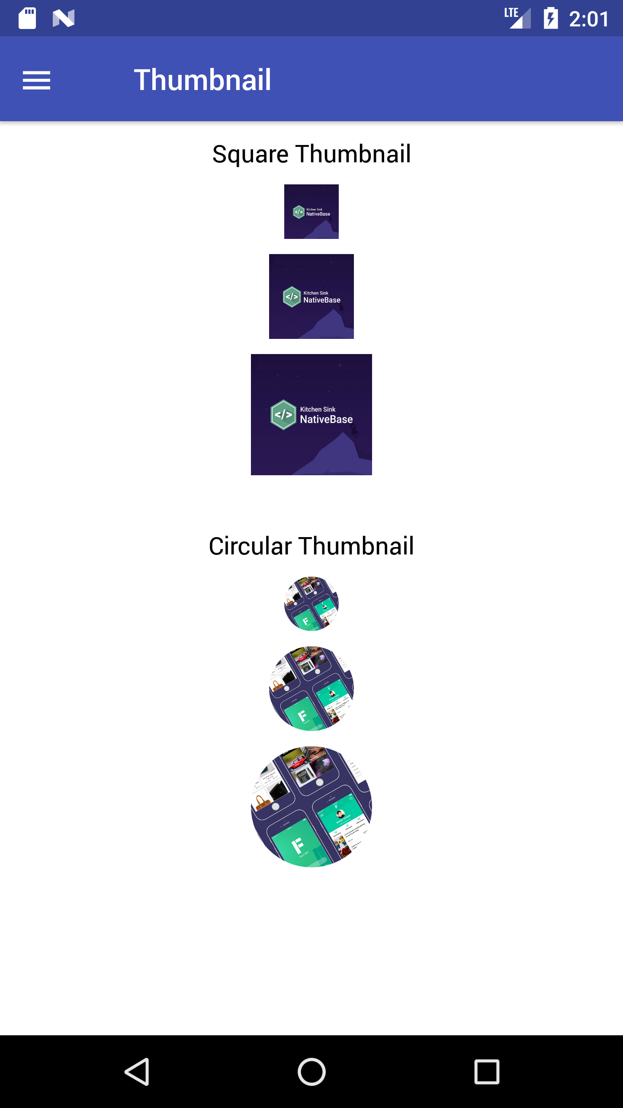
NativeBase-KitchenSink-master/screenshots/android/thumbnail.png
