RhythmSyed/HMD/NativeBase-KitchenSink-master/screenshots/android/toast-duration.gif

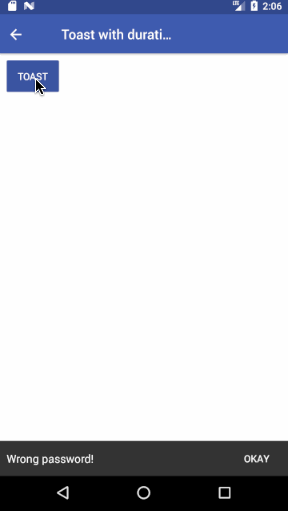
NativeBase-KitchenSink-master/screenshots/android/toast-duration.gif
