RhythmSyed/HMD/NativeBase-KitchenSink-master/screenshots/android/toast-type.gif

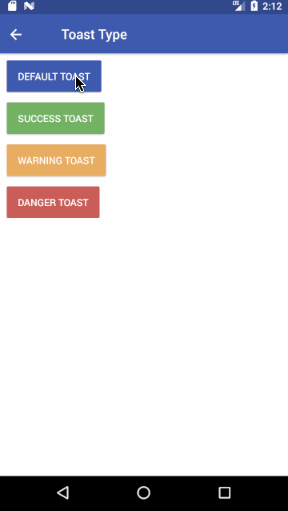
NativeBase-KitchenSink-master/screenshots/android/toast-type.gif
