RhythmSyed/HMD/NativeBase-KitchenSink-master/screenshots/android/typography.png

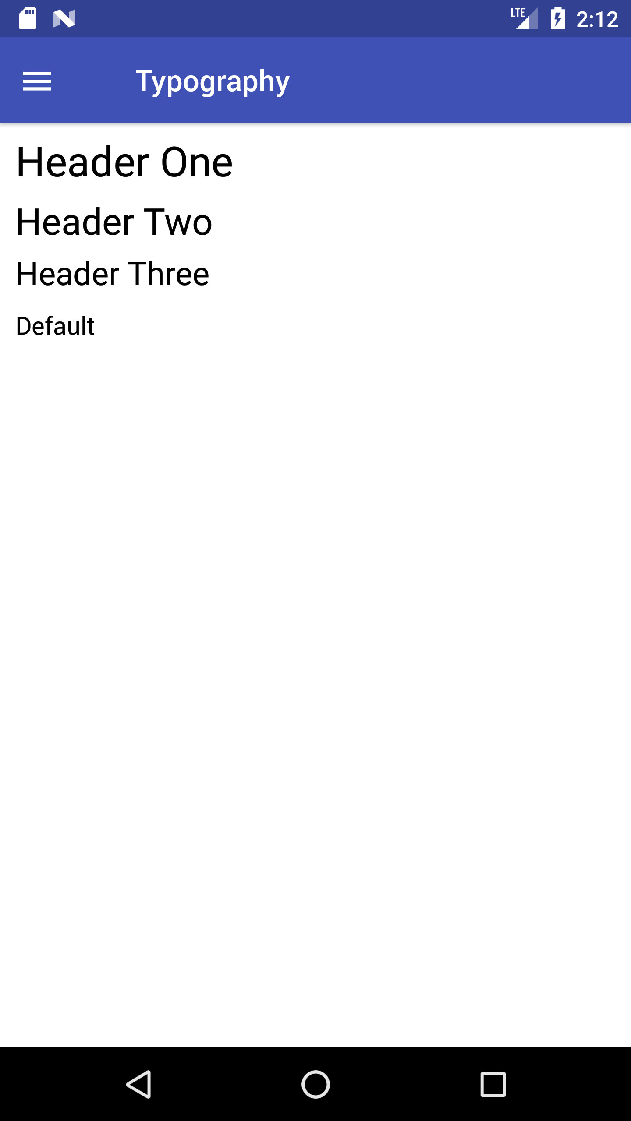
NativeBase-KitchenSink-master/screenshots/android/typography.png
