RhythmSyed/HMD/NativeBase-KitchenSink-master/screenshots/ios/accordion-custom-header-content.gif

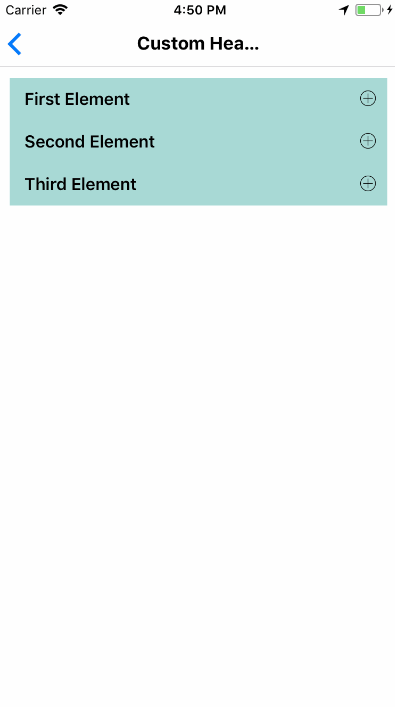
NativeBase-KitchenSink-master/screenshots/ios/accordion-custom-header-content.gif
