RhythmSyed/HMD/NativeBase-KitchenSink-master/screenshots/ios/accordion.gif

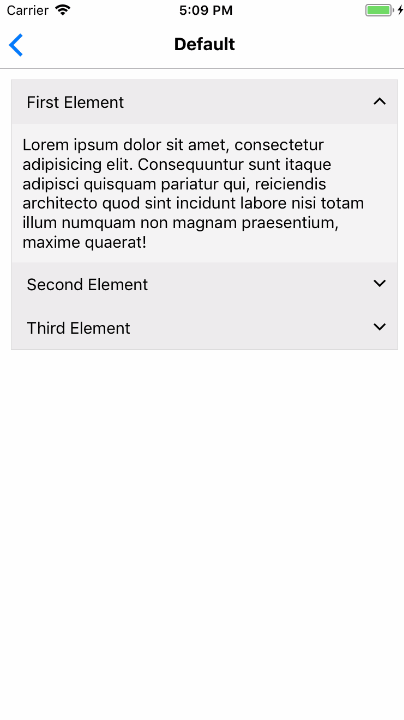
NativeBase-KitchenSink-master/screenshots/ios/accordion.gif
