RhythmSyed/HMD/NativeBase-KitchenSink-master/screenshots/ios/actionsheet.gif

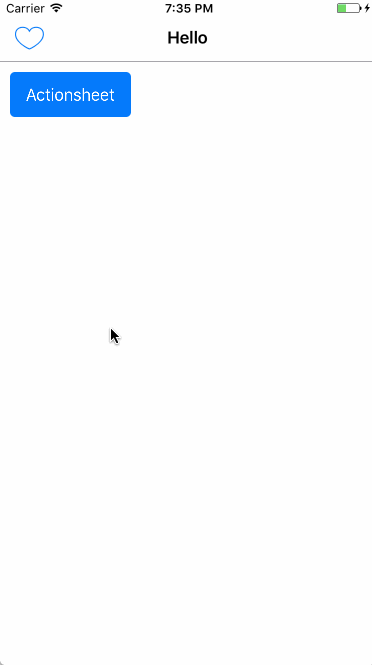
NativeBase-KitchenSink-master/screenshots/ios/actionsheet.gif
