RhythmSyed/HMD/NativeBase-KitchenSink-master/screenshots/ios/anatomy.png

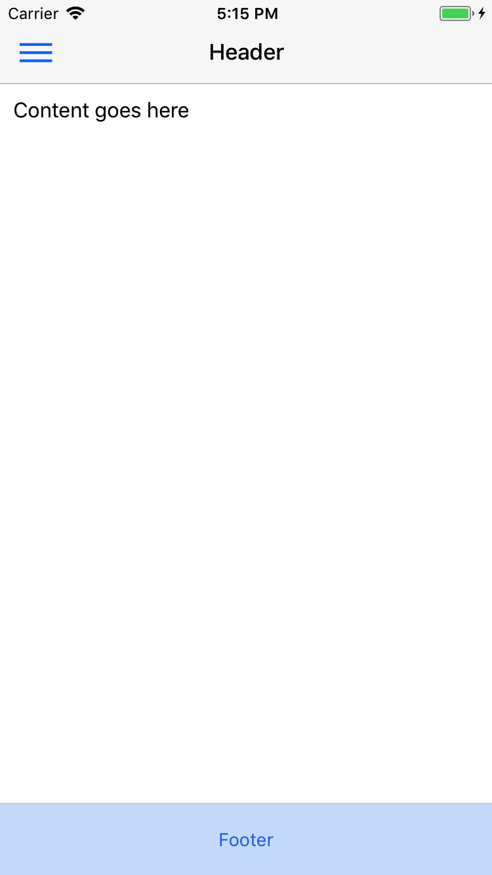
NativeBase-KitchenSink-master/screenshots/ios/anatomy.png
