RhythmSyed/HMD/NativeBase-KitchenSink-master/screenshots/ios/button-block.png

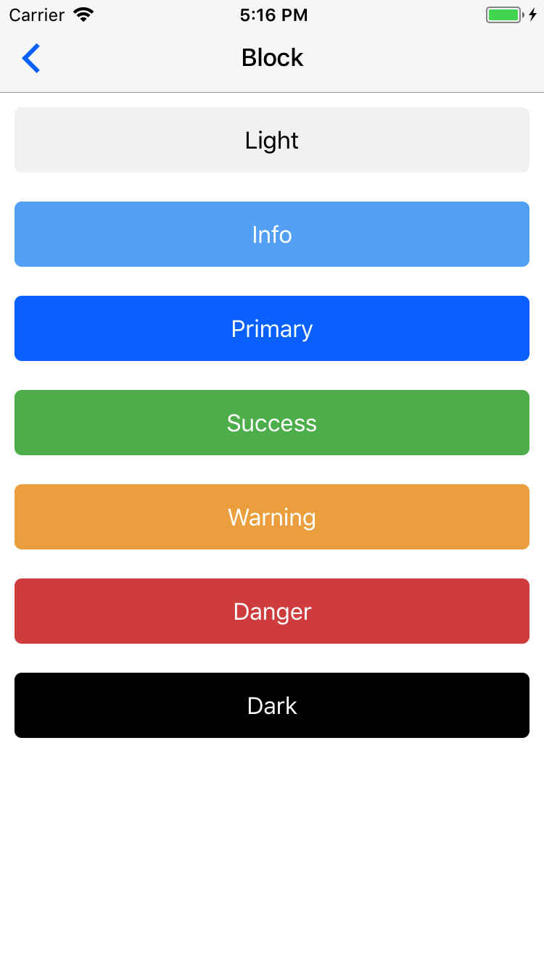
NativeBase-KitchenSink-master/screenshots/ios/button-block.png
