RhythmSyed/HMD/NativeBase-KitchenSink-master/screenshots/ios/button-disabled.png

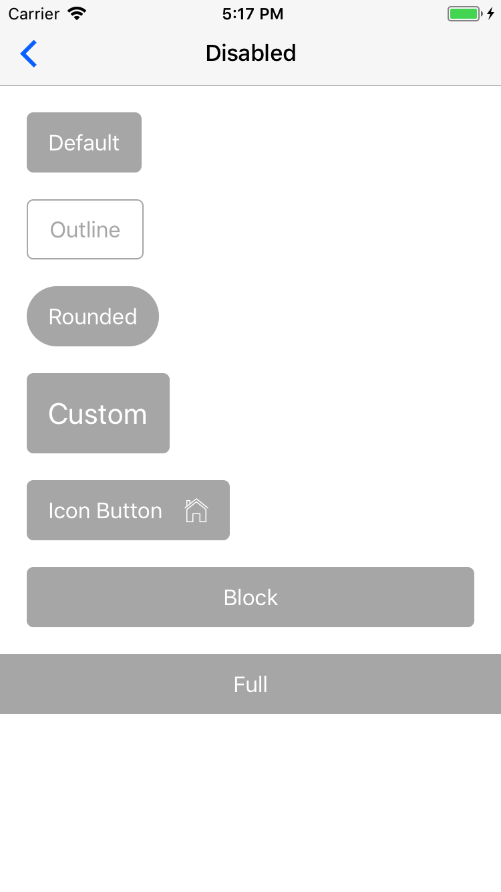
NativeBase-KitchenSink-master/screenshots/ios/button-disabled.png
