RhythmSyed/HMD/NativeBase-KitchenSink-master/screenshots/ios/button-full.png

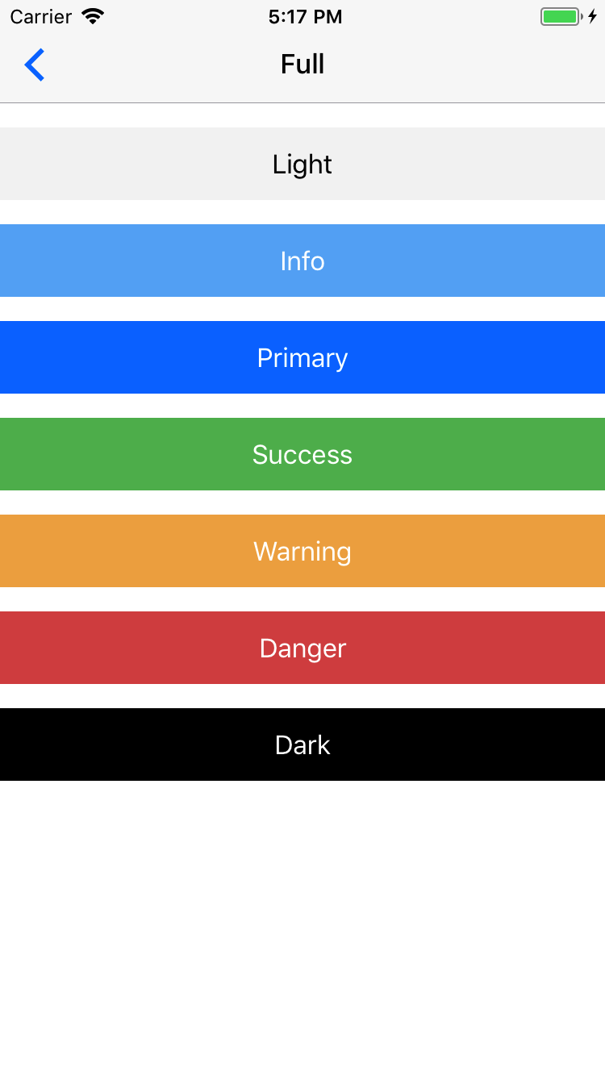
NativeBase-KitchenSink-master/screenshots/ios/button-full.png
