RhythmSyed/HMD/NativeBase-KitchenSink-master/screenshots/ios/button-outline.png

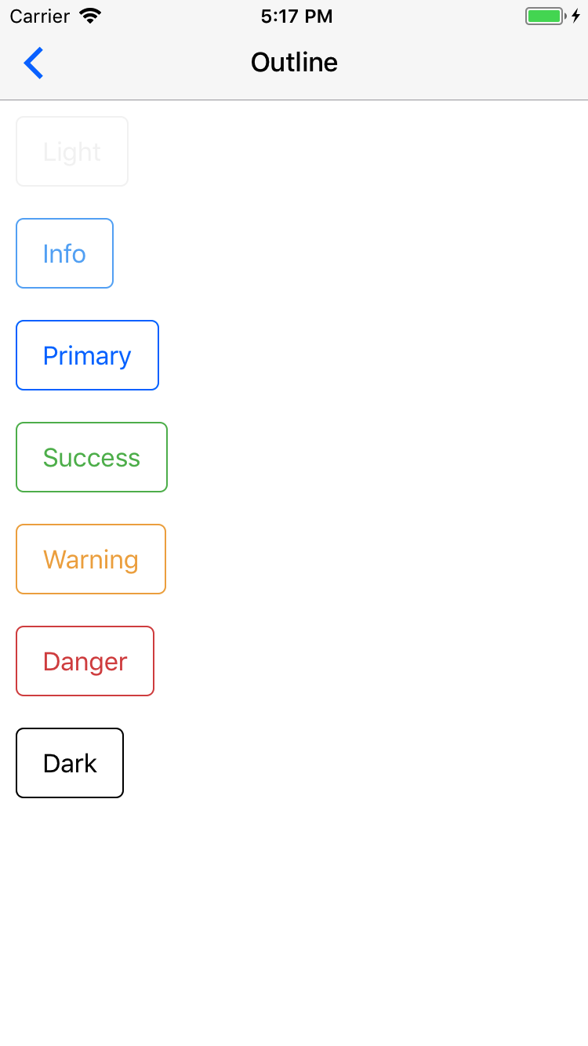
NativeBase-KitchenSink-master/screenshots/ios/button-outline.png
