RhythmSyed/HMD/NativeBase-KitchenSink-master/screenshots/ios/button-size.png

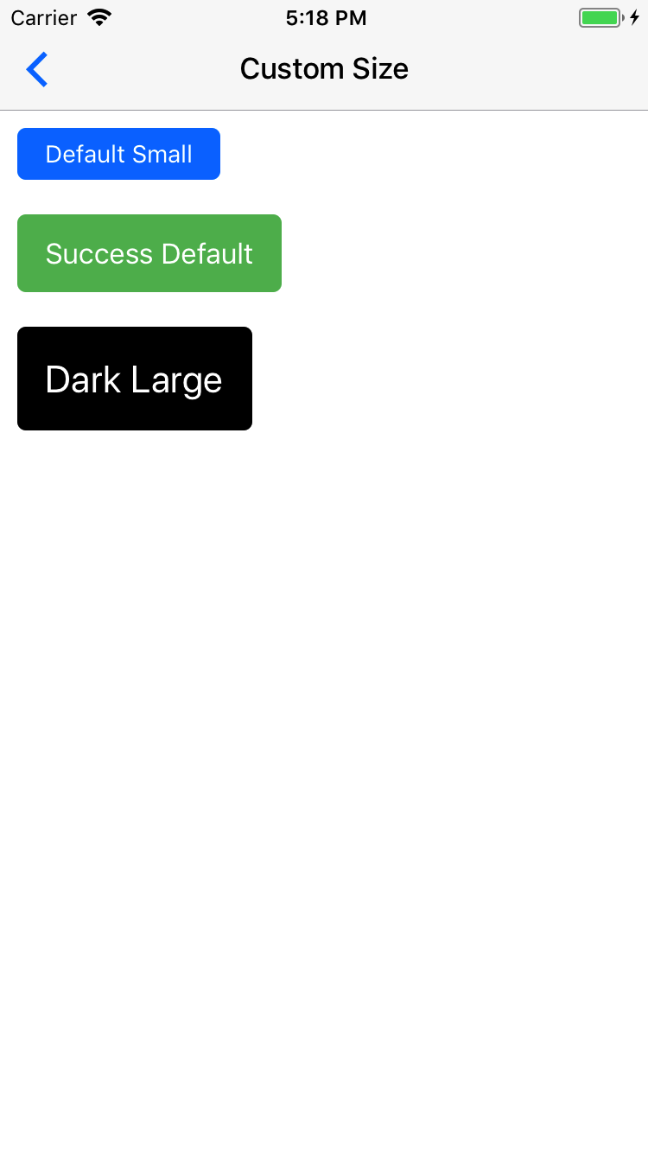
NativeBase-KitchenSink-master/screenshots/ios/button-size.png
