RhythmSyed/HMD/NativeBase-KitchenSink-master/screenshots/ios/card-basic.png

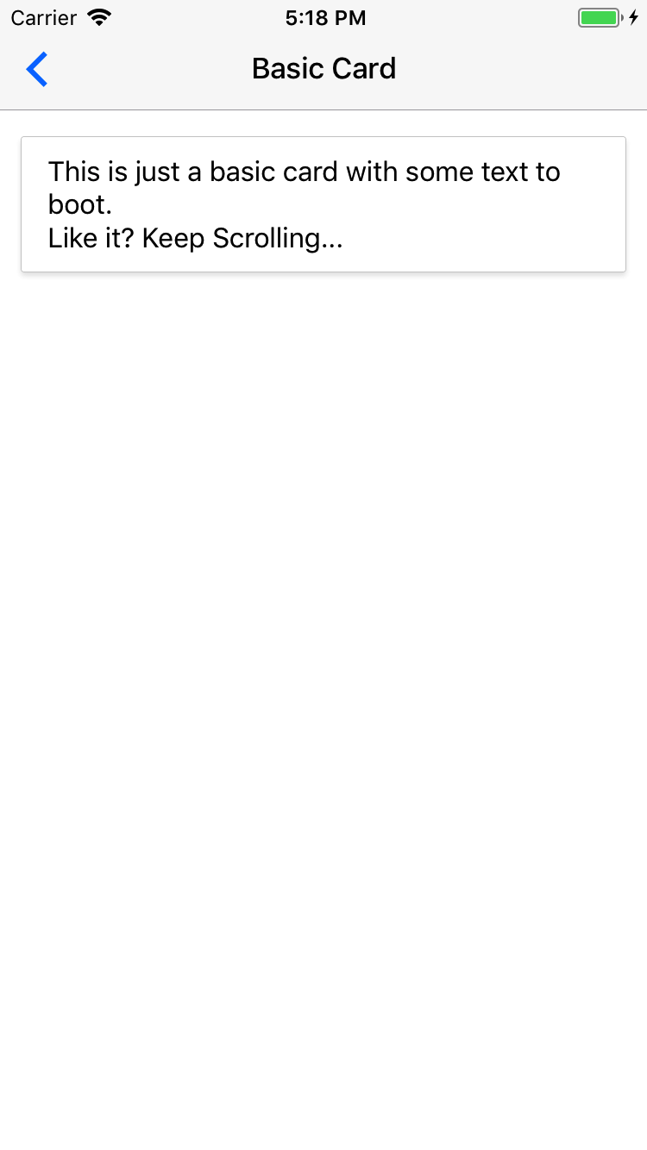
NativeBase-KitchenSink-master/screenshots/ios/card-basic.png
