RhythmSyed/HMD/NativeBase-KitchenSink-master/screenshots/ios/card-bordered.png

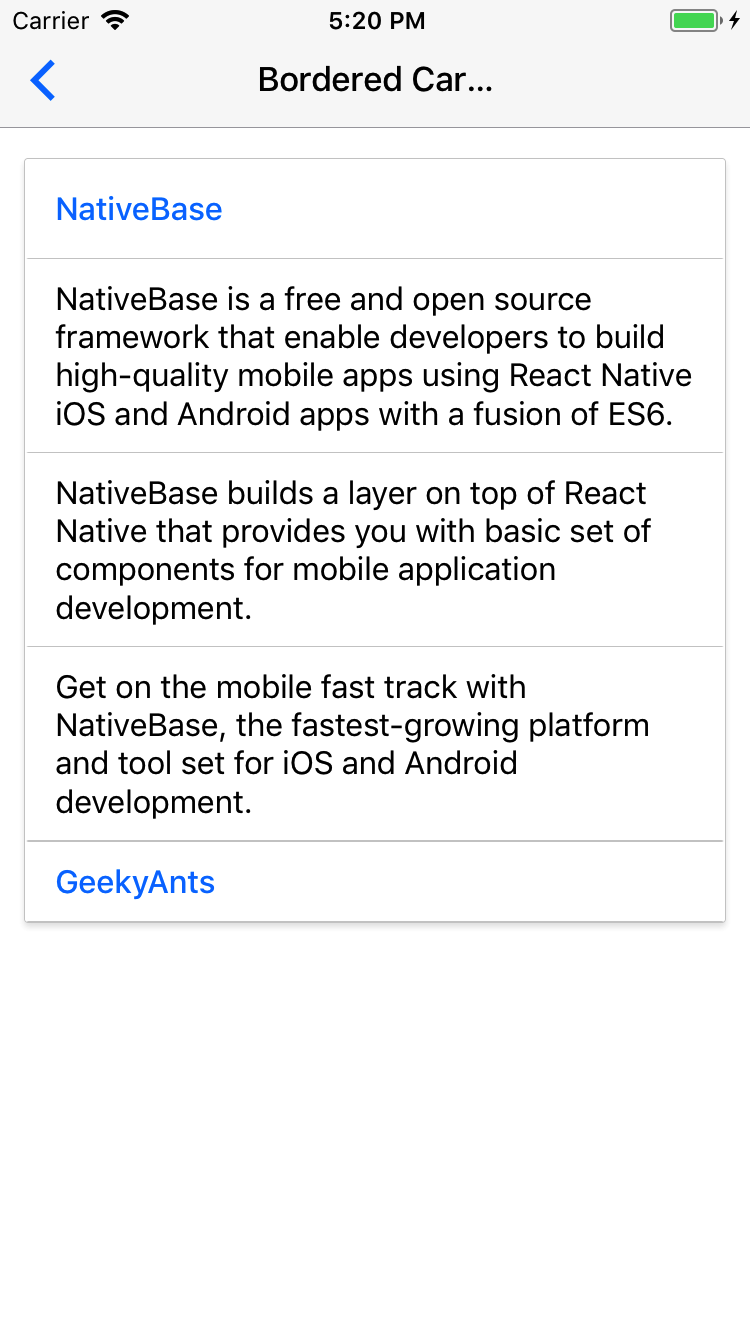
NativeBase-KitchenSink-master/screenshots/ios/card-bordered.png
