RhythmSyed/HMD/NativeBase-KitchenSink-master/screenshots/ios/card-button.gif

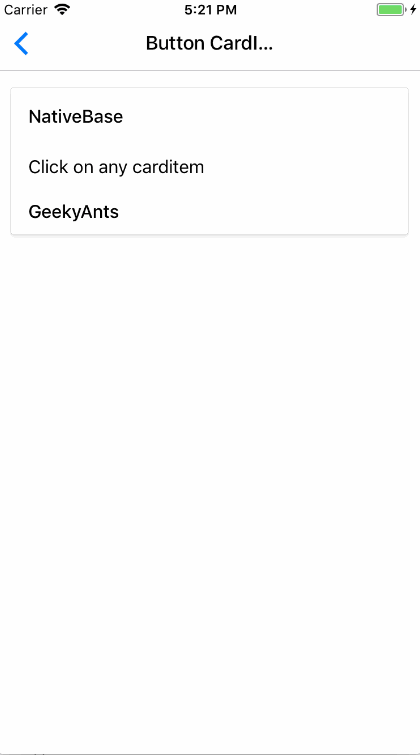
NativeBase-KitchenSink-master/screenshots/ios/card-button.gif
