RhythmSyed/HMD/NativeBase-KitchenSink-master/screenshots/ios/card-image.png

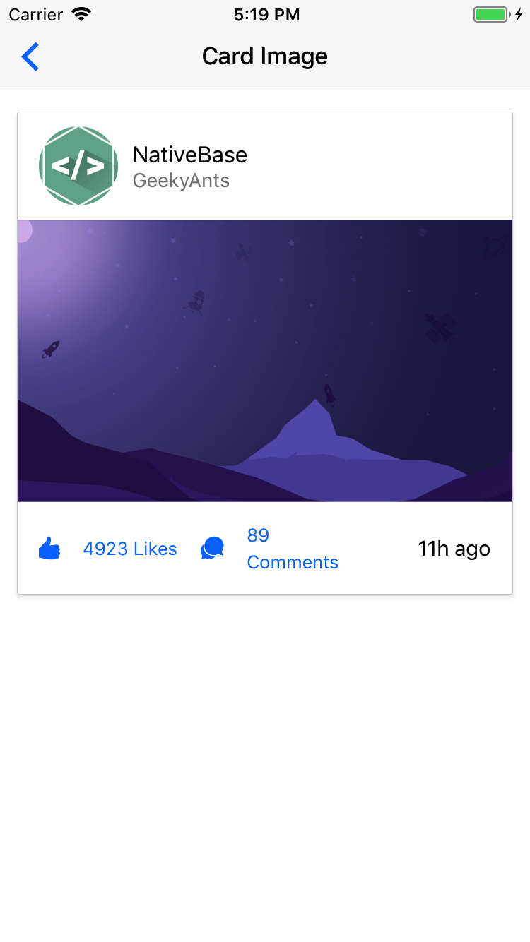
NativeBase-KitchenSink-master/screenshots/ios/card-image.png
