RhythmSyed/HMD/NativeBase-KitchenSink-master/screenshots/ios/card-list.png

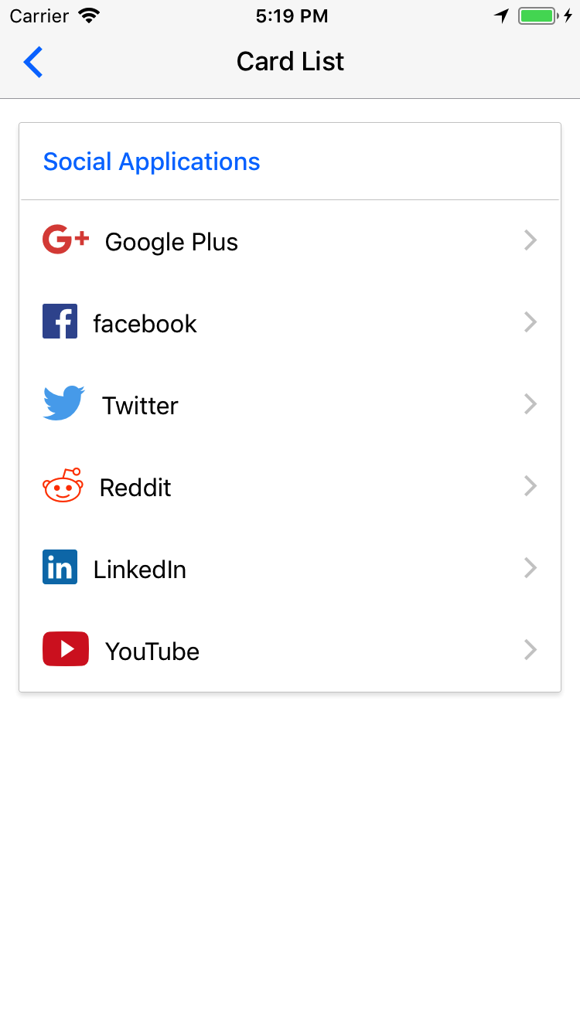
NativeBase-KitchenSink-master/screenshots/ios/card-list.png
