RhythmSyed/HMD/NativeBase-KitchenSink-master/screenshots/ios/card-showcase.png

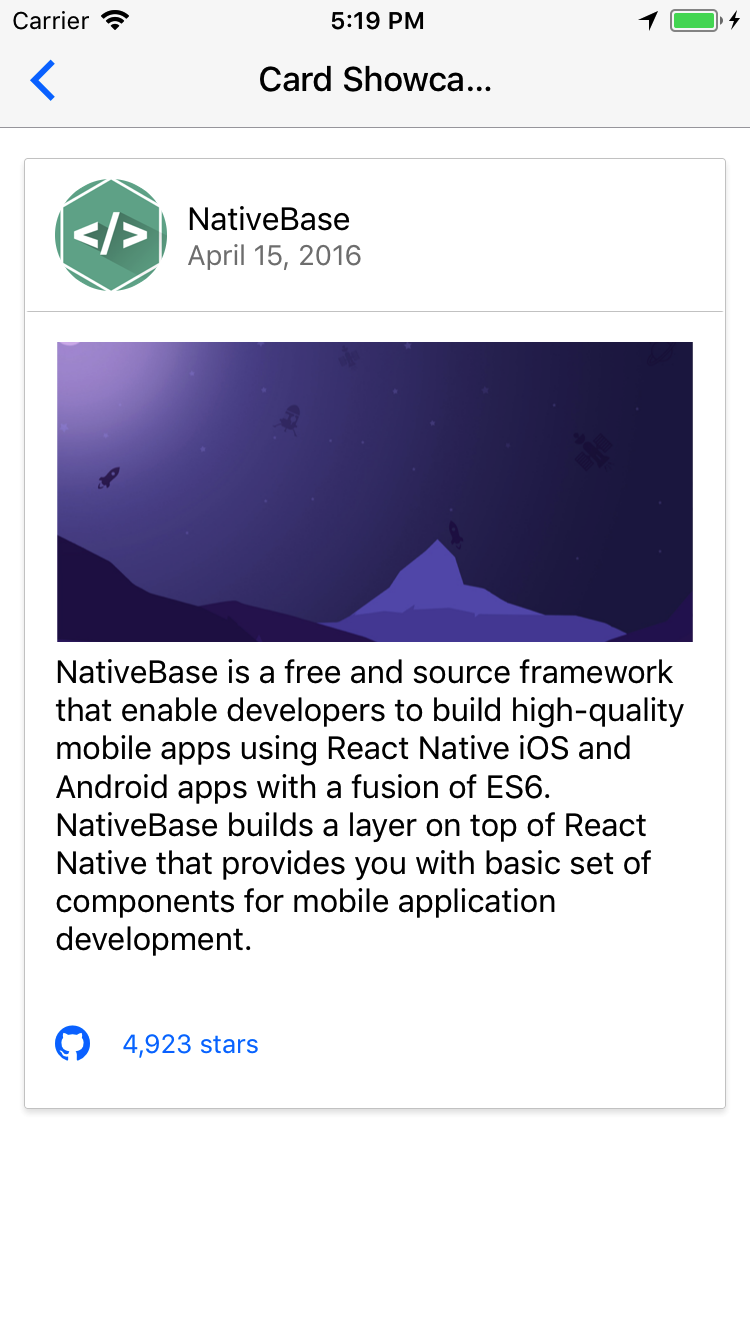
NativeBase-KitchenSink-master/screenshots/ios/card-showcase.png
