RhythmSyed/HMD/NativeBase-KitchenSink-master/screenshots/ios/checkbox.png

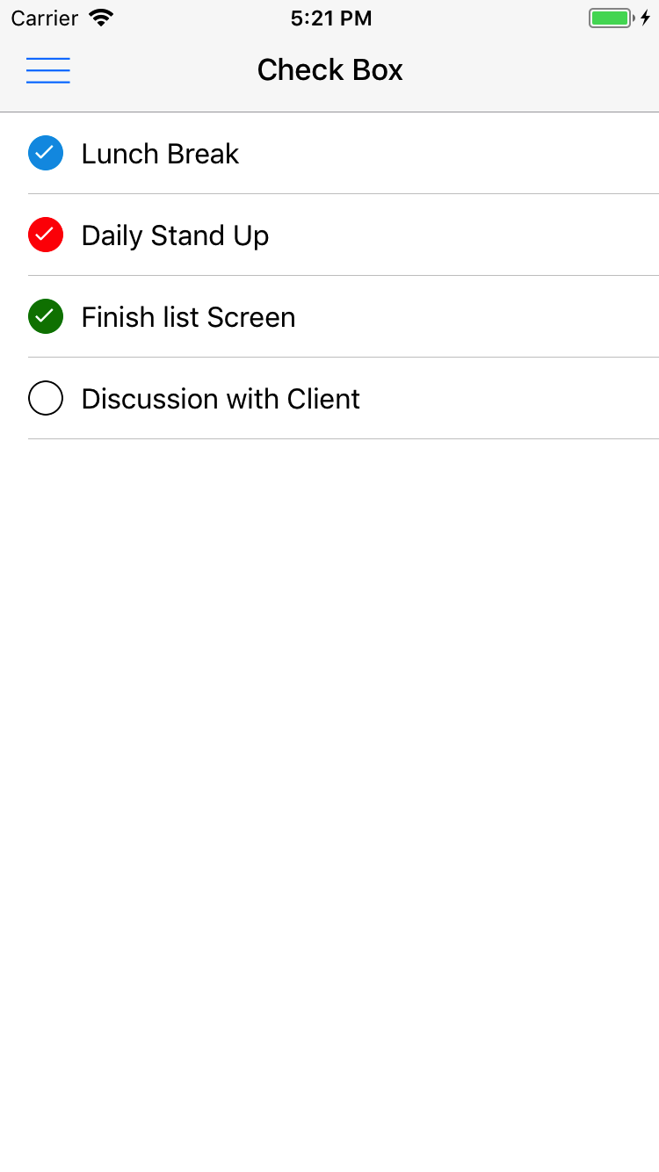
NativeBase-KitchenSink-master/screenshots/ios/checkbox.png
