RhythmSyed/HMD/NativeBase-KitchenSink-master/screenshots/ios/deckswiper-advanced.gif

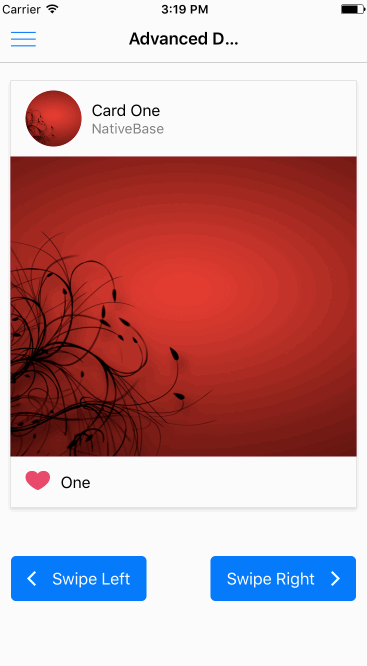
NativeBase-KitchenSink-master/screenshots/ios/deckswiper-advanced.gif
