RhythmSyed/HMD/NativeBase-KitchenSink-master/screenshots/ios/deckswiper.gif

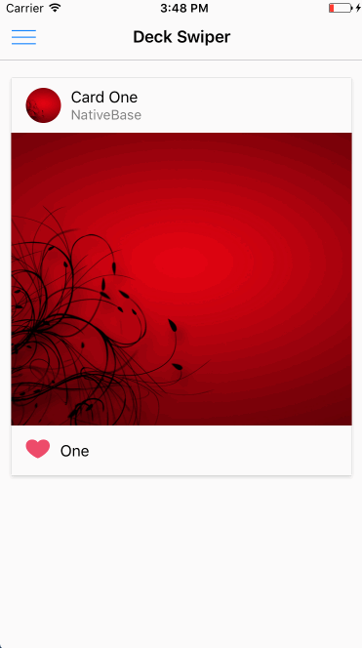
NativeBase-KitchenSink-master/screenshots/ios/deckswiper.gif
