RhythmSyed/HMD/NativeBase-KitchenSink-master/screenshots/ios/drawer.png

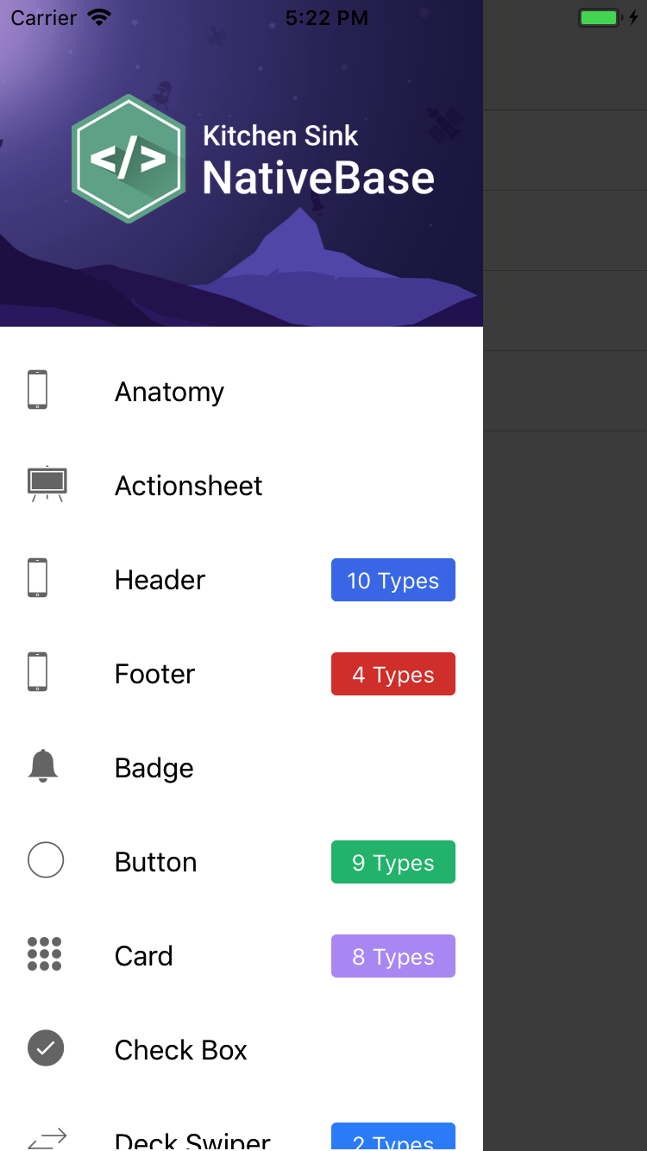
NativeBase-KitchenSink-master/screenshots/ios/drawer.png
