RhythmSyed/HMD/NativeBase-KitchenSink-master/screenshots/ios/FAB-multiple.gif

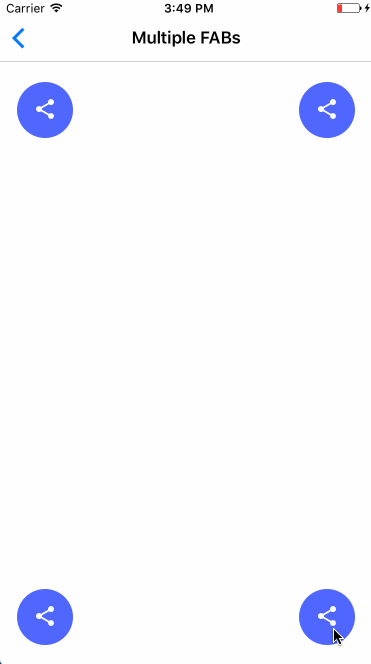
NativeBase-KitchenSink-master/screenshots/ios/FAB-multiple.gif
