RhythmSyed/HMD/NativeBase-KitchenSink-master/screenshots/ios/footer-text.png

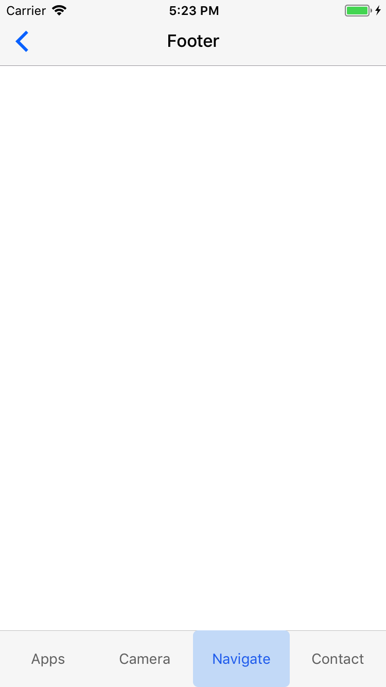
NativeBase-KitchenSink-master/screenshots/ios/footer-text.png
