RhythmSyed/HMD/NativeBase-KitchenSink-master/screenshots/ios/header-custom.png

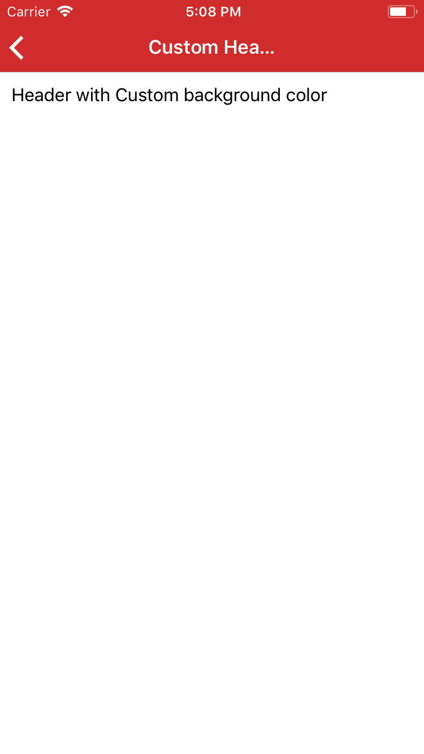
NativeBase-KitchenSink-master/screenshots/ios/header-custom.png
