RhythmSyed/HMD/NativeBase-KitchenSink-master/screenshots/ios/header-with-title-and-subtitle.png

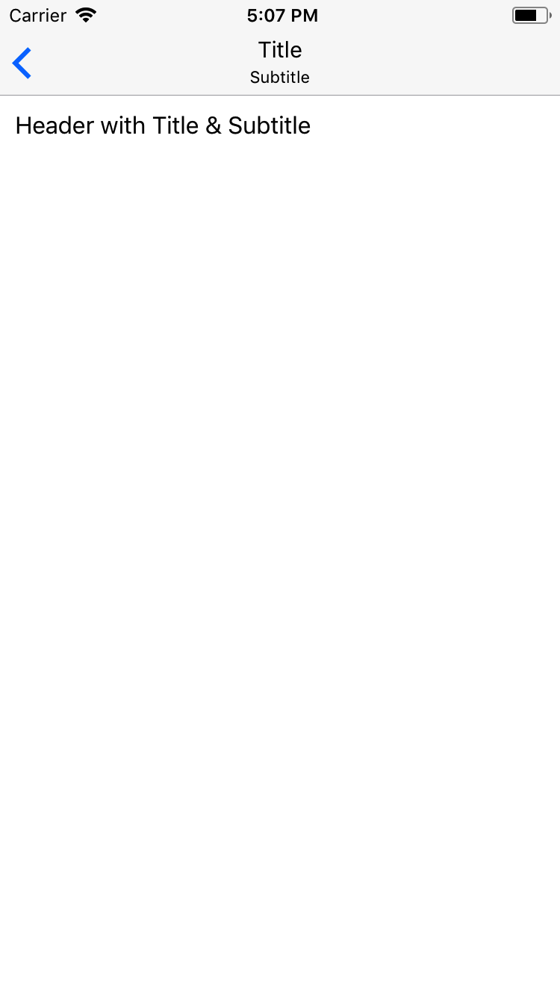
NativeBase-KitchenSink-master/screenshots/ios/header-with-title-and-subtitle.png
