RhythmSyed/HMD/NativeBase-KitchenSink-master/screenshots/ios/input-fixed.png

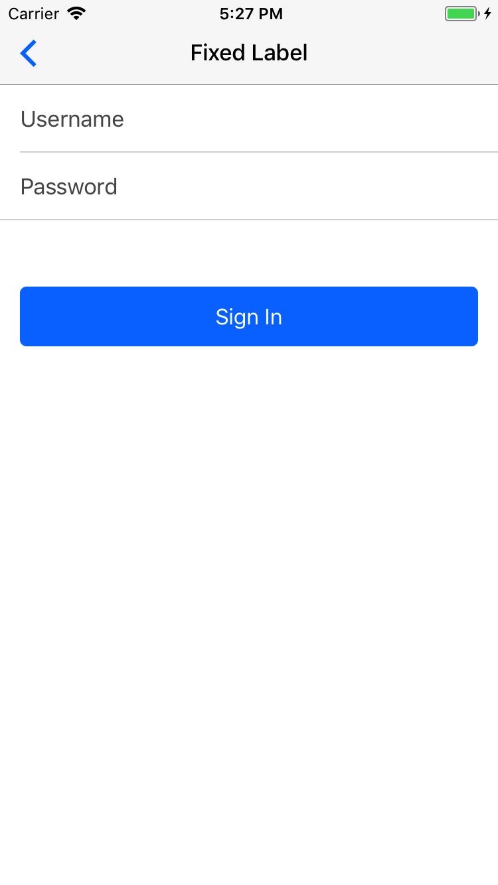
NativeBase-KitchenSink-master/screenshots/ios/input-fixed.png
