RhythmSyed/HMD/NativeBase-KitchenSink-master/screenshots/ios/input-picker.gif

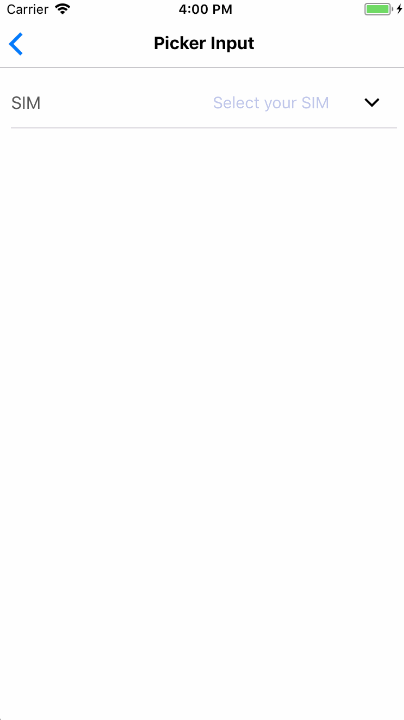
NativeBase-KitchenSink-master/screenshots/ios/input-picker.gif
