RhythmSyed/HMD/NativeBase-KitchenSink-master/screenshots/ios/list-basic.png

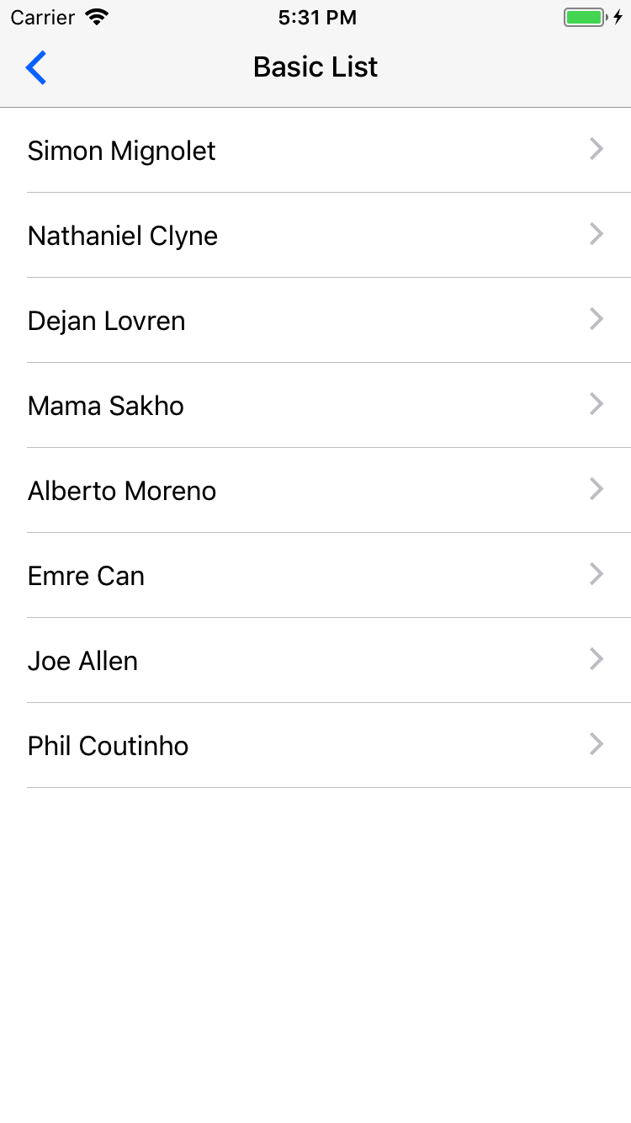
NativeBase-KitchenSink-master/screenshots/ios/list-basic.png
