RhythmSyed/HMD/NativeBase-KitchenSink-master/screenshots/ios/list-divider.png

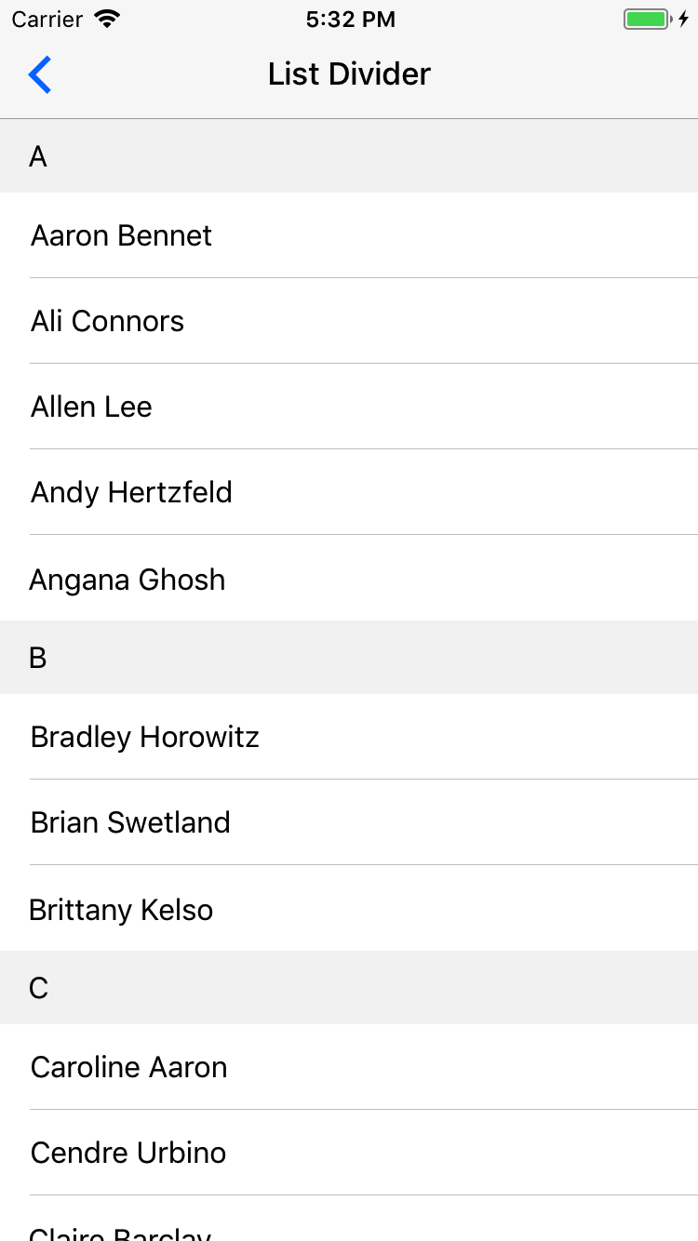
NativeBase-KitchenSink-master/screenshots/ios/list-divider.png
