RhythmSyed/HMD/NativeBase-KitchenSink-master/screenshots/ios/list-header.png

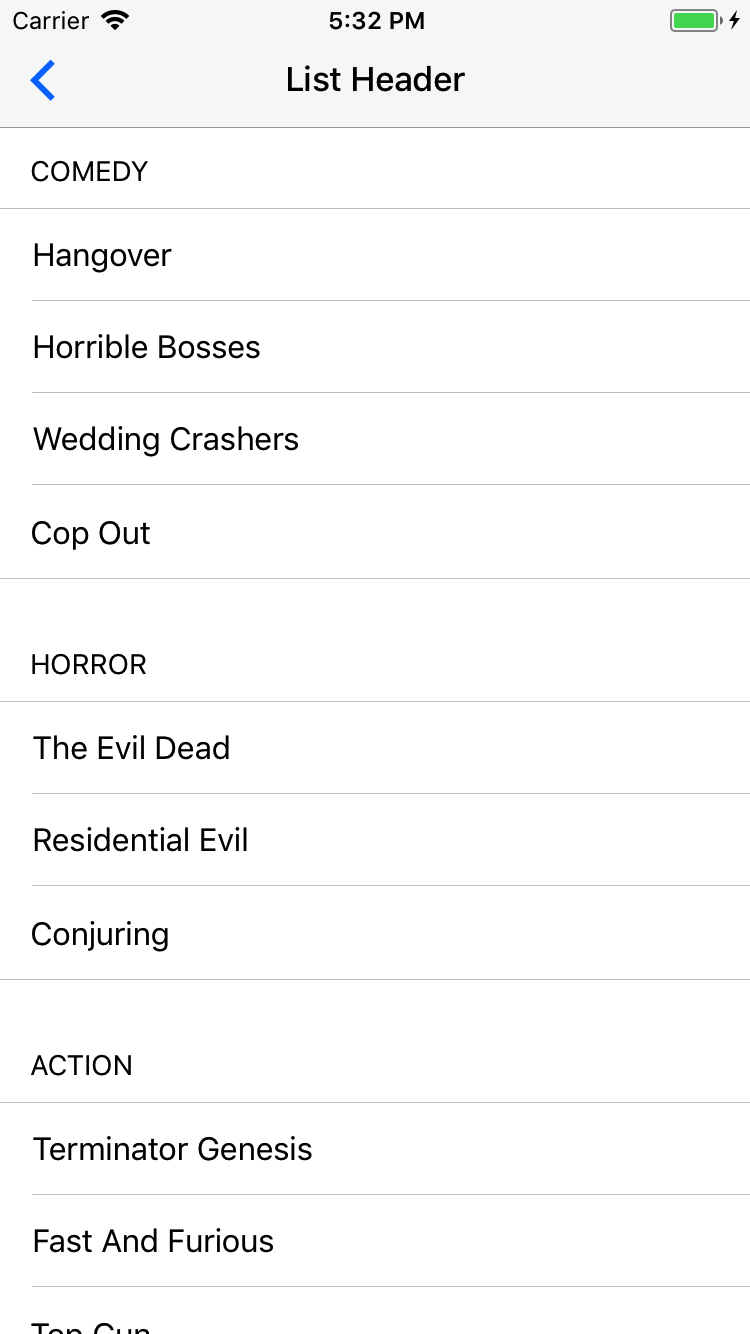
NativeBase-KitchenSink-master/screenshots/ios/list-header.png
