RhythmSyed/HMD/NativeBase-KitchenSink-master/screenshots/ios/list-separator.png

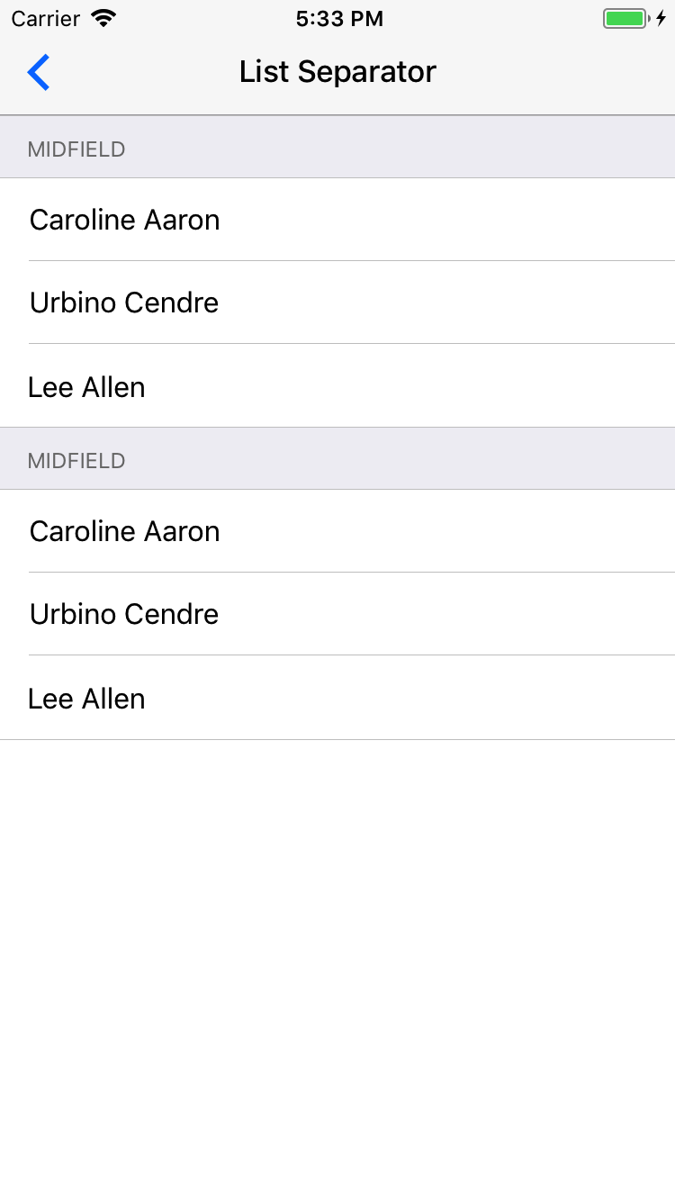
NativeBase-KitchenSink-master/screenshots/ios/list-separator.png
