RhythmSyed/HMD/NativeBase-KitchenSink-master/screenshots/ios/list-swipe-single-row-custom-style.gif

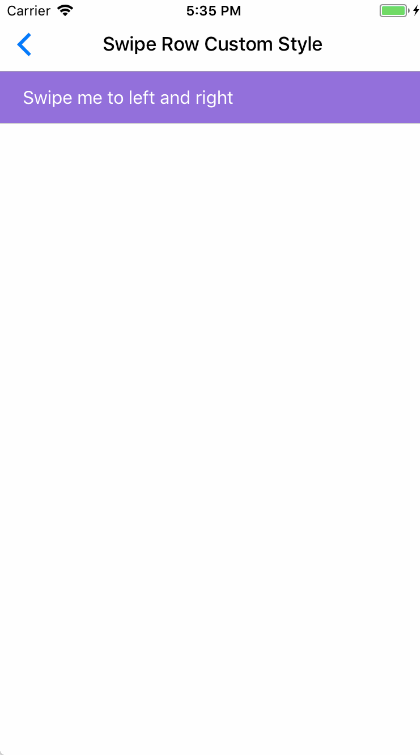
NativeBase-KitchenSink-master/screenshots/ios/list-swipe-single-row-custom-style.gif
