RhythmSyed/HMD/NativeBase-KitchenSink-master/screenshots/ios/list-swipe-single-row.gif

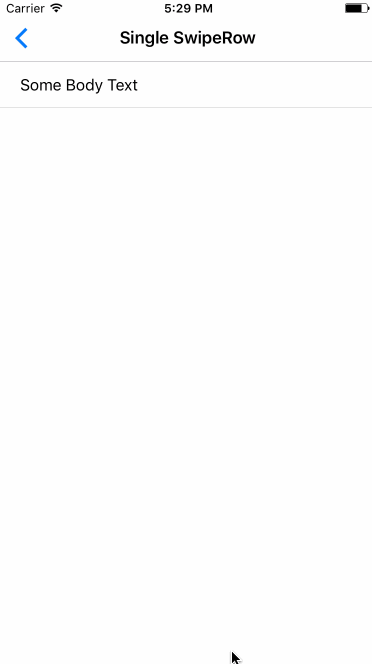
NativeBase-KitchenSink-master/screenshots/ios/list-swipe-single-row.gif
