RhythmSyed/HMD/NativeBase-KitchenSink-master/screenshots/ios/list-thumbnail.png

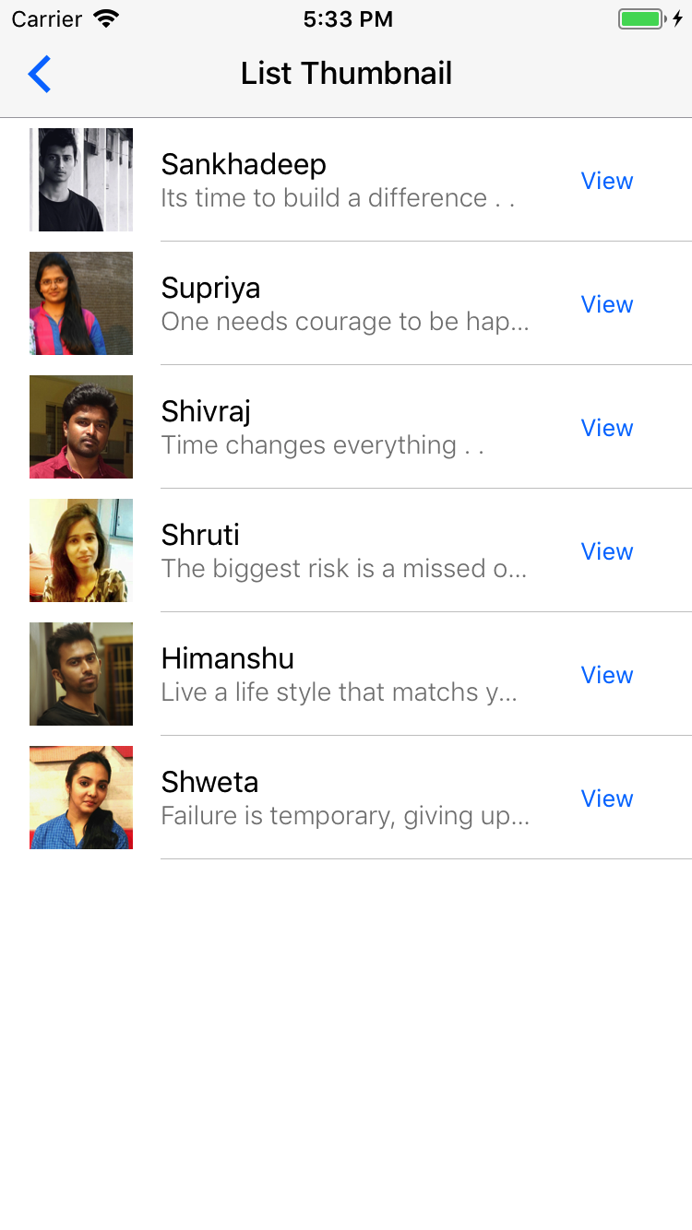
NativeBase-KitchenSink-master/screenshots/ios/list-thumbnail.png
