RhythmSyed/HMD/NativeBase-KitchenSink-master/screenshots/ios/picker-text-itemtext-style.gif

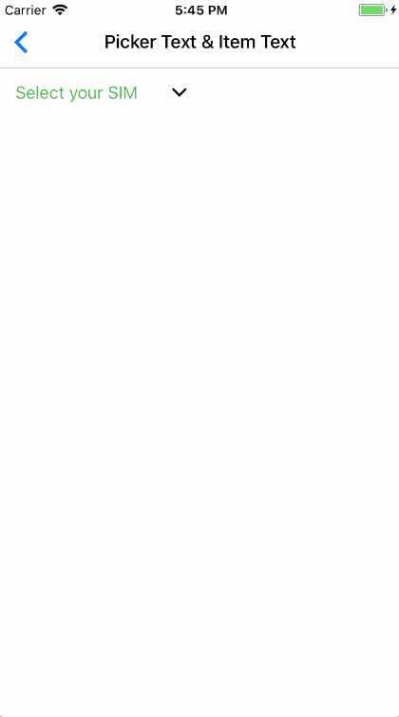
NativeBase-KitchenSink-master/screenshots/ios/picker-text-itemtext-style.gif
