RhythmSyed/HMD/NativeBase-KitchenSink-master/screenshots/ios/radio-custom.png

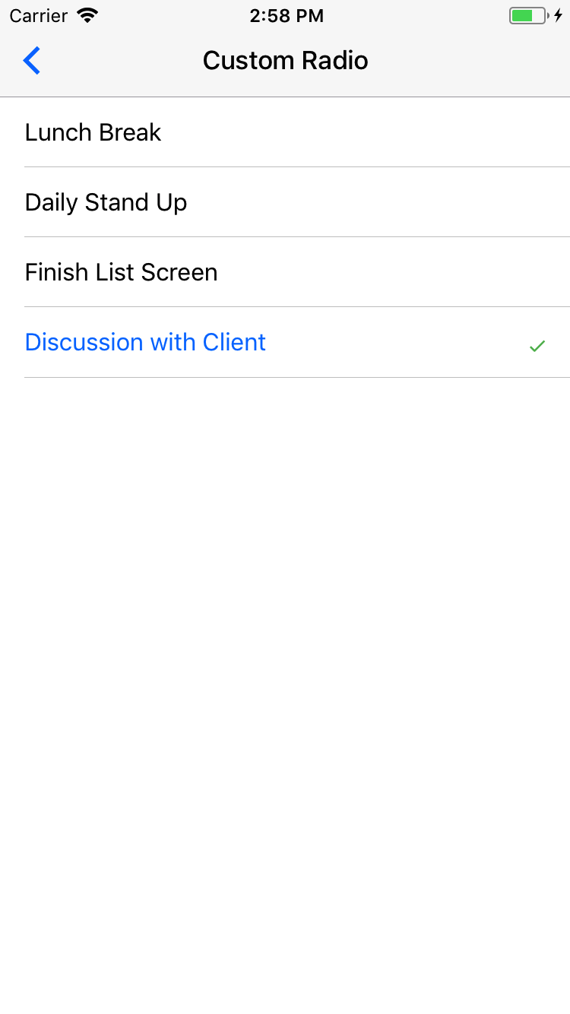
NativeBase-KitchenSink-master/screenshots/ios/radio-custom.png
