RhythmSyed/HMD/NativeBase-KitchenSink-master/screenshots/ios/searchbar.png

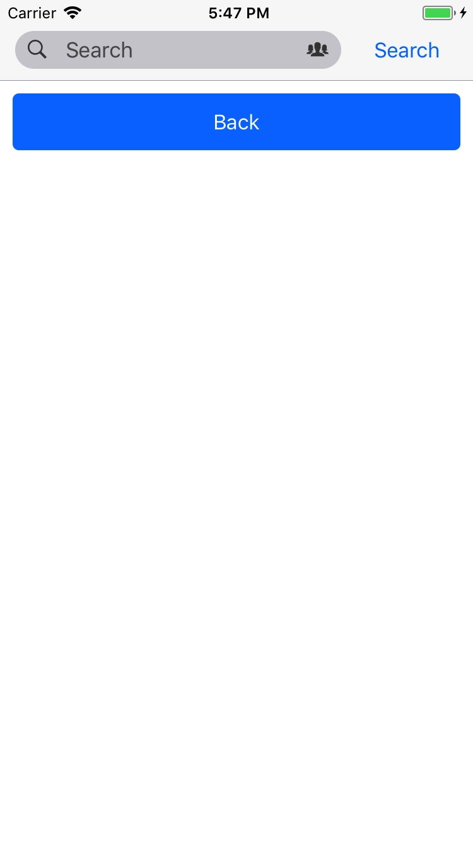
NativeBase-KitchenSink-master/screenshots/ios/searchbar.png
