RhythmSyed/HMD/NativeBase-KitchenSink-master/screenshots/ios/segment-outside-header.gif

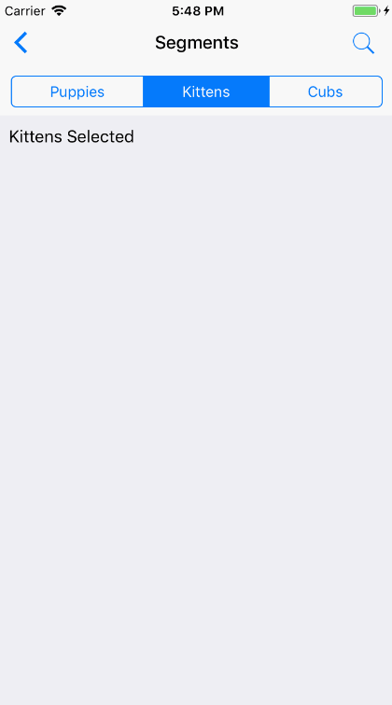
NativeBase-KitchenSink-master/screenshots/ios/segment-outside-header.gif
