RhythmSyed/HMD/NativeBase-KitchenSink-master/screenshots/ios/spinner.gif

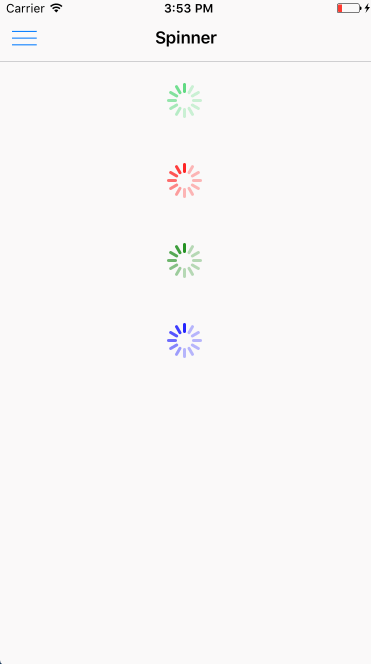
NativeBase-KitchenSink-master/screenshots/ios/spinner.gif
