RhythmSyed/HMD/NativeBase-KitchenSink-master/screenshots/ios/tabs-advanced.gif

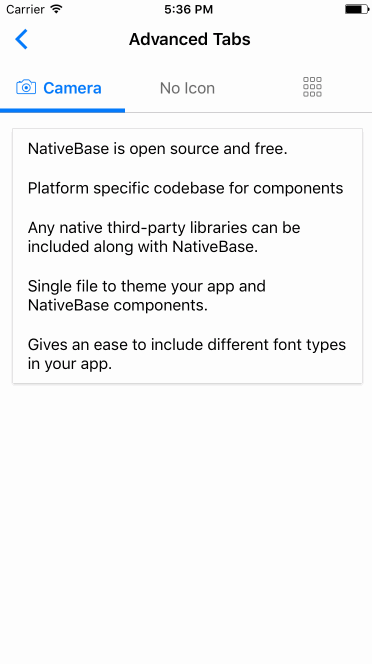
NativeBase-KitchenSink-master/screenshots/ios/tabs-advanced.gif
