RhythmSyed/HMD/NativeBase-KitchenSink-master/screenshots/ios/thumbnail.png

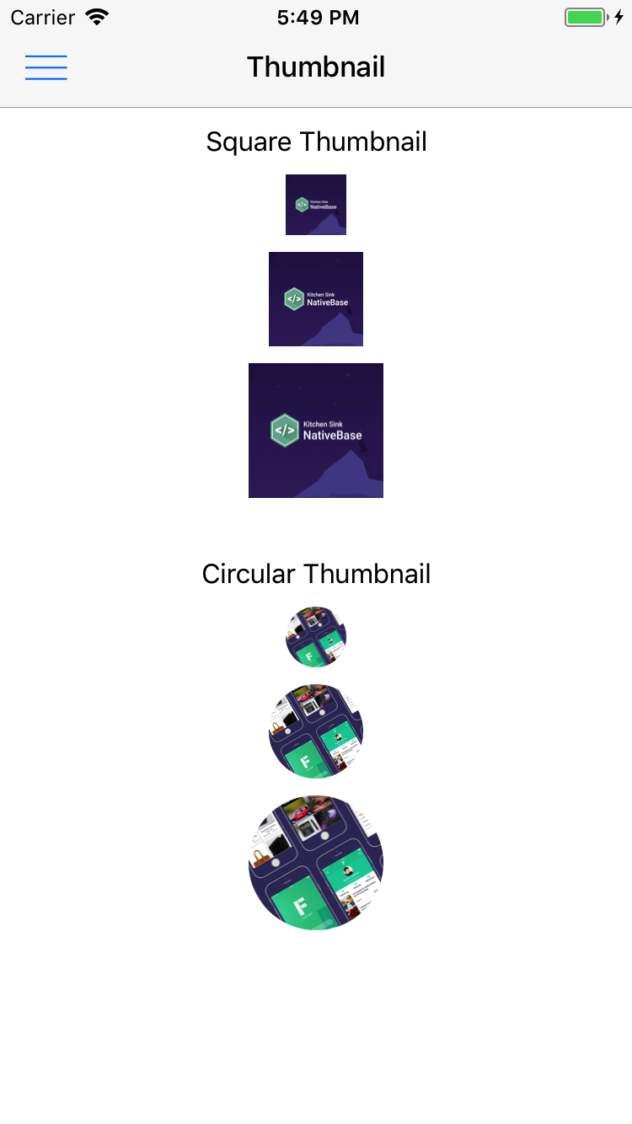
NativeBase-KitchenSink-master/screenshots/ios/thumbnail.png
