RhythmSyed/HMD/NativeBase-KitchenSink-master/screenshots/ios/toast-type.gif

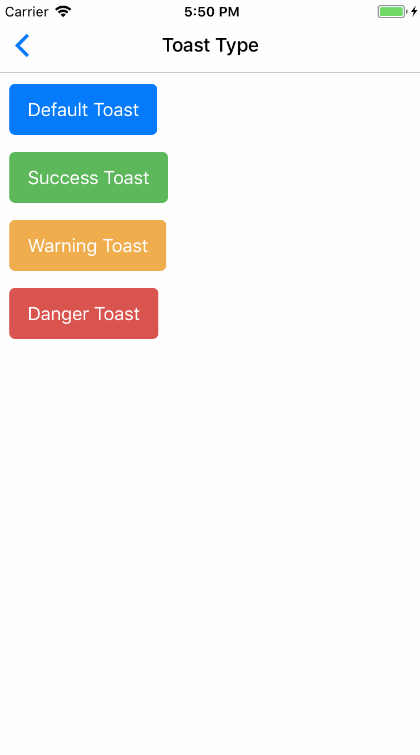
NativeBase-KitchenSink-master/screenshots/ios/toast-type.gif
