RhythmSyed/HMD/firmware/main/imagedata.c

#include "features.h"

/* Width 37 Height: 50 */
const unsigned char GIMAGE_Z[250] = { /* 0X00,0X01,0X25,0X00,0X32,0X00, */
0X00,0X00,0X00,0X00,0X00,0X00,0X00,0X00,0X00,0X00,0X1F,0XFF,0XFF,0XFF,0XC0,0X1F,
0XFF,0XFF,0XFF,0XC0,0X1F,0XF0,0X00,0X3F,0X80,0X1F,0X00,0X00,0X7F,0X00,0X1E,0X00,
0X00,0X7F,0X00,0X1C,0X00,0X00,0XFE,0X00,0X3C,0X00,0X01,0XFE,0X00,0X38,0X00,0X01,
0XFC,0X00,0X38,0X00,0X03,0XF8,0X00,0X38,0X00,0X03,0XF8,0X00,0X38,0X00,0X07,0XF0,
0X00,0X30,0X00,0X0F,0XE0,0X00,0X30,0X00,0X0F,0XE0,0X00,0X00,0X00,0X1F,0XC0,0X00,
0X00,0X00,0X3F,0XC0,0X00,0X00,0X00,0X3F,0X80,0X00,0X00,0X00,0X7F,0X00,0X00,0X00,
0X00,0X7F,0X00,0X00,0X00,0X00,0XFE,0X00,0X00,0X00,0X01,0XFC,0X00,0X00,0X00,0X01,
0XFC,0X00,0X00,0X00,0X03,0XF8,0X00,0X00,0X00,0X03,0XF8,0X00,0X00,0X00,0X07,0XF0,
0X00,0X00,0X00,0X0F,0XE0,0X00,0X00,0X00,0X0F,0XE0,0X00,0X00,0X00,0X1F,0XC0,0X00,
0X00,0X00,0X1F,0X80,0X00,0X00,0X00,0X3F,0X80,0X00,0X00,0X00,0X7F,0X00,0X00,0X00,
0X00,0X7F,0X00,0X00,0XC0,0X00,0XFE,0X00,0X00,0XC0,0X01,0XFC,0X00,0X00,0XC0,0X01,
0XFC,0X00,0X00,0XC0,0X03,0XF8,0X00,0X01,0XC0,0X03,0XF0,0X00,0X01,0XC0,0X07,0XF0,
0X00,0X01,0XC0,0X0F,0XE0,0X00,0X03,0XC0,0X0F,0XE0,0X00,0X03,0XC0,0X1F,0XC0,0X00,
0X07,0XC0,0X1F,0X80,0X00,0X0F,0XC0,0X3F,0X80,0X00,0X3F,0XC0,0X7F,0X00,0X0F,0XFF,
0XC0,0X7F,0XFF,0XFF,0XFF,0XC0,0X7F,0XFF,0XFF,0XFF,0XC0,0X00,0X00,0X00,0X00,0X00,
0X00,0X00,0X00,0X00,0X00,0X00,0X00,0X00,0X00,0X00,};


/* Width 45 Height: 16 */
const unsigned char GIMAGE_HMD[96] = { /* 0X00,0X01,0X2D,0X00,0X10,0X00, */
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
0X00,0X7E,0X00,0X00,0X00,0X00,0X00,0X00,0X7E,0X00,0X00,0X00,0X00,0X00,0X00,0X7E,
0X00,0X00,0X00,0X00,0X00,0X00,0X7E,0X00,0X00,0X00,0X00,0X00,0X00,0X7E,0X00,0X00,
0X00,0X00,0X00,0X00,0X3E,0X00,0X00,0X00,0X00,0X00,0X00,0X1C,0X00,0X00,};
